abbyniewchas/heart_valve_bioreactor/designs/Full System CAD/Pressure Sensor V2/Assem3.PNG

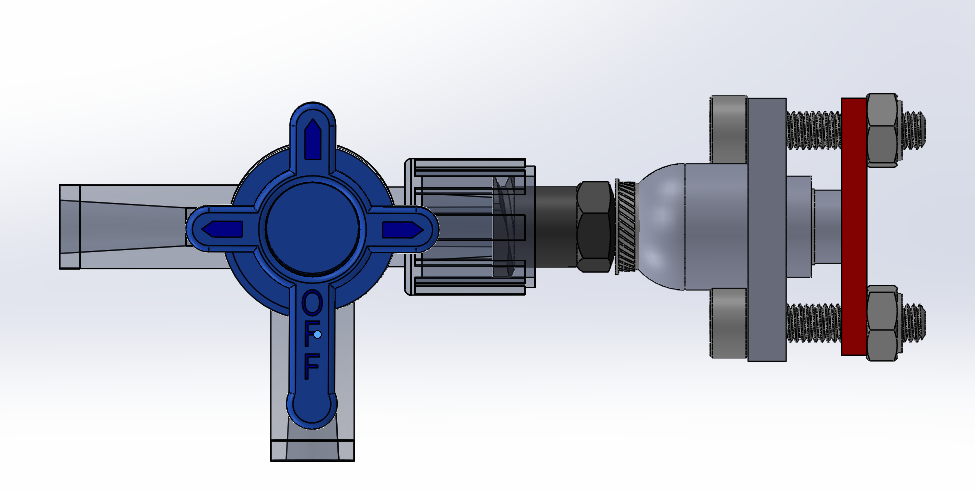
designs/Full System CAD/Pressure Sensor V2/Assem3.PNG
