abbyniewchas/heart_valve_bioreactor/matlab/data_acquisition/waveform_fig.jpg

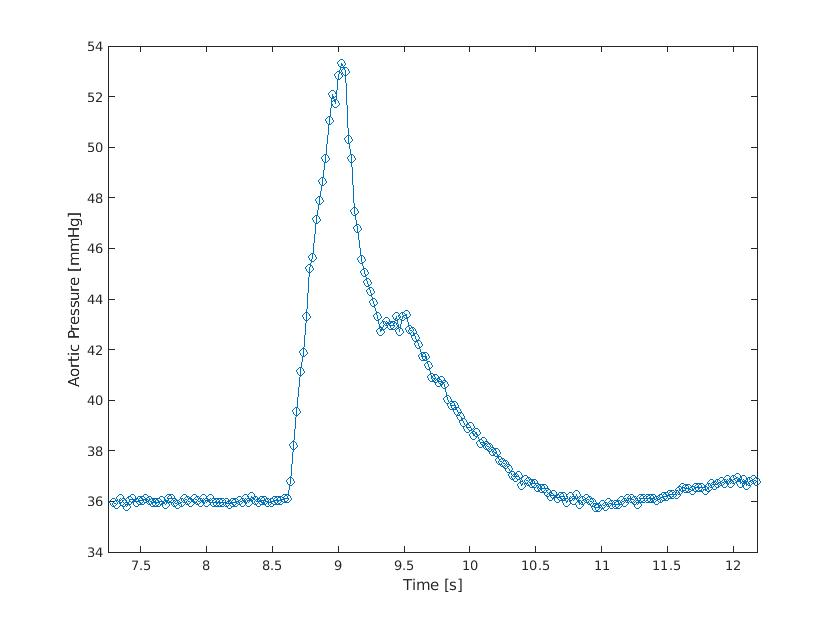
matlab/data_acquisition/waveform_fig.jpg
