abbyniewchas/heart_valve_bioreactor/designs/Full System CAD/Tubing and fittings/Media exchange fittings.SLDASM

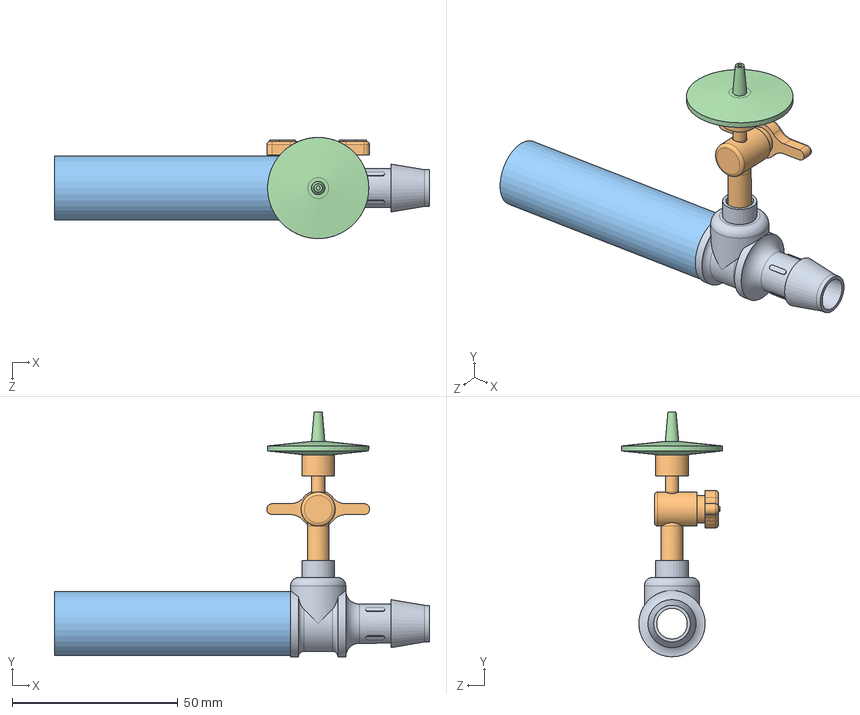
[picture p33: CAD file, 2020-04-21]
designs/Full System CAD/Tubing and fittings/Media exchange fittings.SLDASM
113.0 x 73.7 x 30.5 mm
.5in tubing to .5in tubing to male luer tee fitting
Stopcock (from grabcad)
Check valve to pump
Sterile filter
