abbyniewchas/heart_valve_bioreactor/designs/Full System CAD/Tubing and fittings/Check-ALL valve with fittings.SLDASM

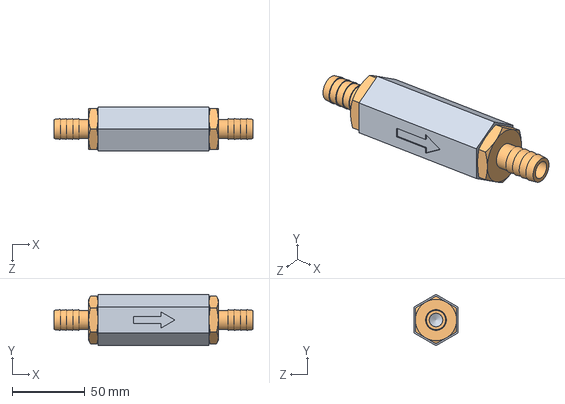
[picture p34: CAD file, 2020-04-21]
designs/Full System CAD/Tubing and fittings/Check-ALL valve with fittings.SLDASM
136.4 x 35.2 x 30.5 mm
Checkk-ALL check valve
three quarter NPT to half in tube x 2
