abbyniewchas/heart_valve_bioreactor/designs/Full System CAD/Current pump/Full pump assembly.SLDASM

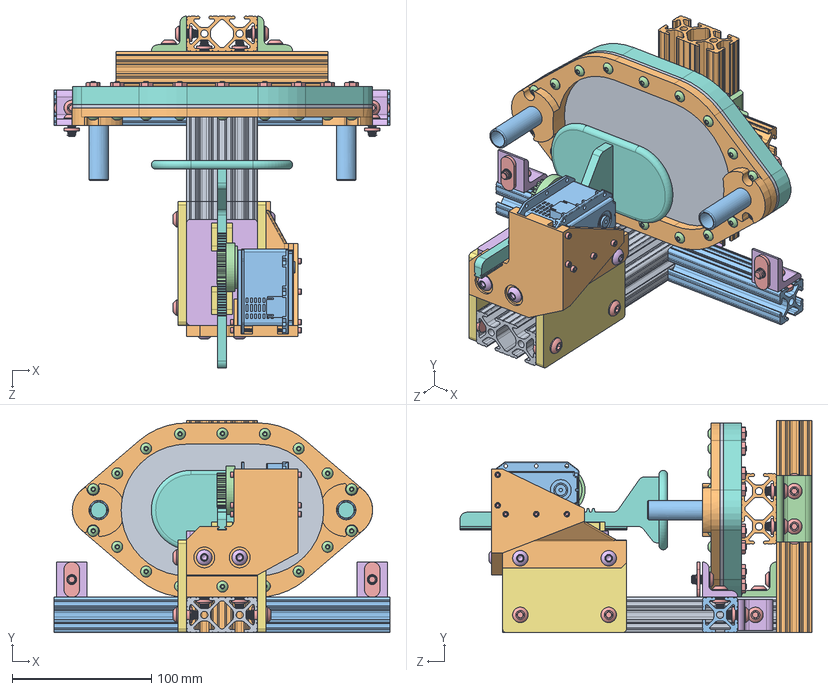
[picture p35: CAD file, 2020-04-21]
designs/Full System CAD/Current pump/Full pump assembly.SLDASM
241.3 x 152.4 x 252.9 mm
47065T418_ALUMINUM T-SLOTTED FRAMING EXTRUSION
80_20 double 6in x 2
80_20 3.75in x 2
80_20 L bracket wide x 3
80_20 fastening screw x 27
80_20 L-bracket small x 4
pump acrylic aligner x 2
Pump membrane backing
Pump membrane
Pump membrane front
Pump membrane fitting x 2
membrane screw x 18
membrane nut x 18
Acrylic topper
rack mount x 2
Pump piston rack
80_20 double 3.5in
Motor mount
MX-64 Motor (from grabacad)
Pump pinion
motor mount screw x 8
.25-20 extra screw x 4
pinion mounting screw
