abbyniewchas/heart_valve_bioreactor/designs/Full System CAD/Pump redesign concept/redesigned piston assembly.SLDASM

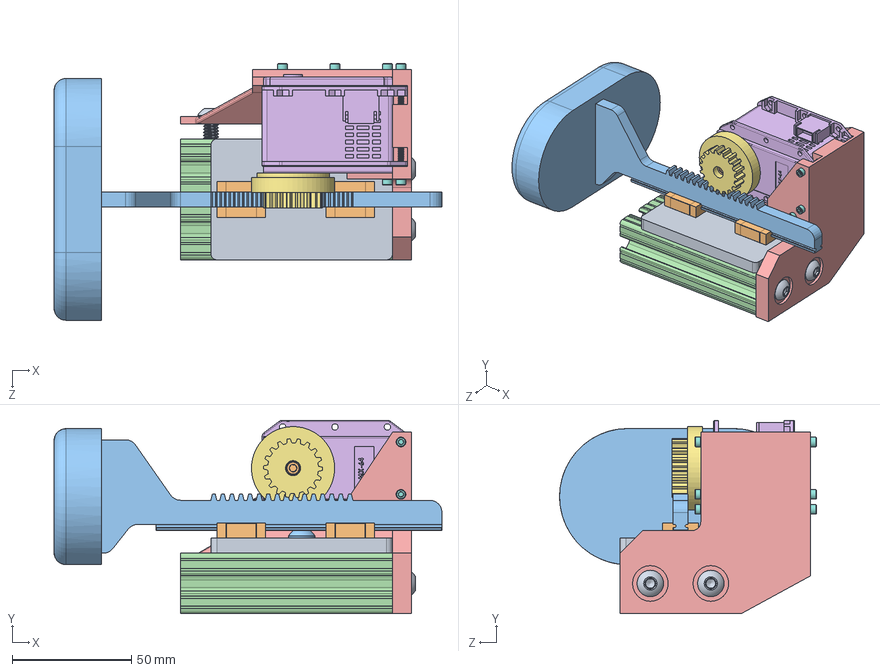
[picture p36: CAD file, 2020-04-21]
designs/Full System CAD/Pump redesign concept/redesigned piston assembly.SLDASM
162.9 x 81.2 x 107.8 mm
Acrylic topper
rack mount x 2
redesigned pump piston rack + paddle
80_20 double 3.5in
Motor mount
MX-64 Motor (from grabacad)
Pump pinion
motor mount screw x 8
.25-20 extra screw x 4
pinion mounting screw
80_20 fastening screw
