abbyniewchas/heart_valve_bioreactor/designs/Full System CAD/Tubing and fittings/Compliance Chamber top fitting.SLDASM

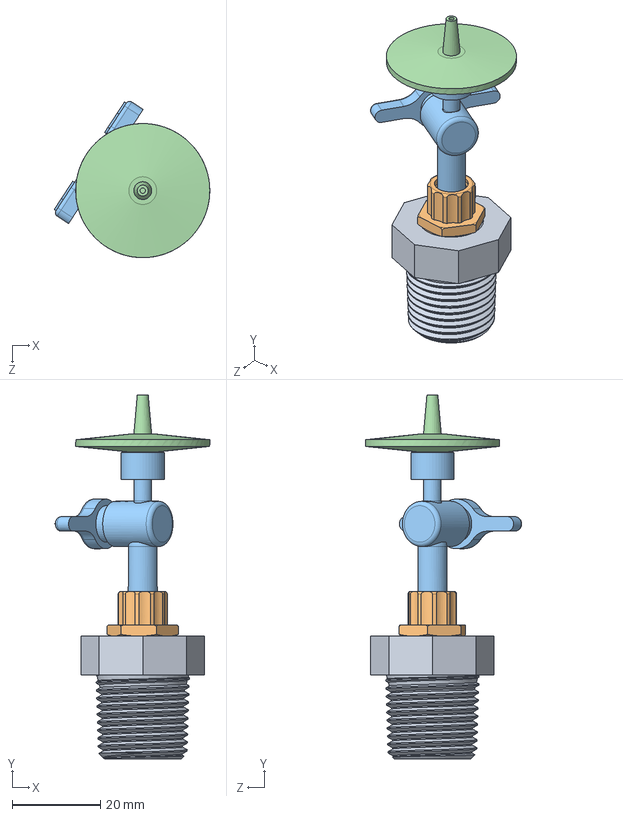
[picture p37: CAD file, 2020-04-21]
designs/Full System CAD/Tubing and fittings/Compliance Chamber top fitting.SLDASM
35.4 x 82.7 x 35.5 mm
4880K343_1-2NPTmale-to-1-4NPTfemale
51525K437_1-4NPT-to-Luer
Stopcock (from grabcad)
Sterile filter
