abbyniewchas/heart_valve_bioreactor/designs/Full System CAD/Frame/MR Mount asm.SLDASM

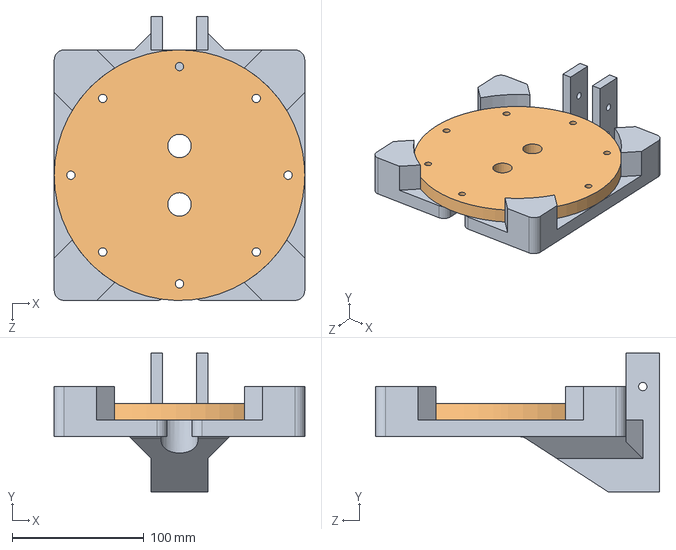
[picture p38: CAD file, 2020-04-21]
designs/Full System CAD/Frame/MR Mount asm.SLDASM
190.5 x 105.4 x 215.9 mm
Media Reservoir Mount
Media reservoir modified bottom
