abbyniewchas/heart_valve_bioreactor/designs/Full System CAD/Pump redesign concept/Redesigned full pump assembly.SLDASM

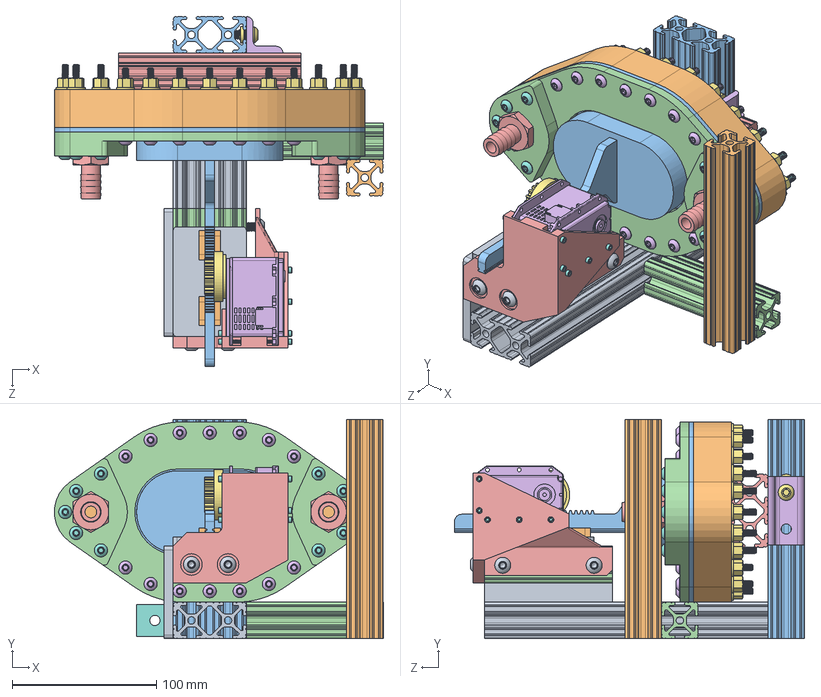
[picture p39: CAD file, 2020-04-21]
designs/Full System CAD/Pump redesign concept/Redesigned full pump assembly.SLDASM
228.5 x 152.4 x 243.0 mm
redesigned pump membrane backing
redesigned pump membrane
redesigned membrane front
half NPT to half in tube x 2
91255A252_membrane screw x 14
membrane nut 10_24 x 24
91255A813_membrane screw long x 10
Acrylic topper
rack mount x 2
redesigned pump piston rack + paddle
80_20 double 3.5in
Motor mount
MX-64 Motor (from grabacad)
Pump pinion
motor mount screw x 8
.25-20 extra screw x 4
pinion mounting screw
80_20 fastening screw
