abbyniewchas/heart_valve_bioreactor/designs/Full System CAD/Frame/80_20 Frame.SLDASM

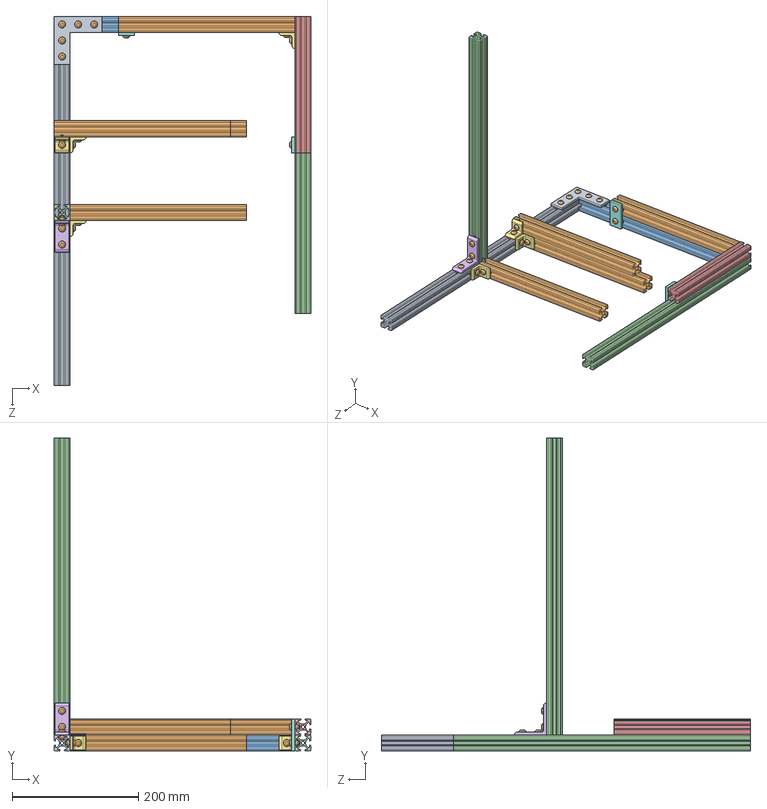
[picture p40: CAD file, 2020-04-21]
designs/Full System CAD/Frame/80_20 Frame.SLDASM
406.4 x 495.3 x 584.2 mm
80_20 23in
80_20 11in x 4
80_20 14in
80_20 18.5in x 2
80_20 8.5in
80_20 L Bracket long
80_20 L-bracket small x 4
80_20 straight fastener x 2
80_20 Corner fastener
80_20 fastening screw x 21
