abbyniewchas/heart_valve_bioreactor/designs/Full System CAD/Frame/CC mount am.SLDASM

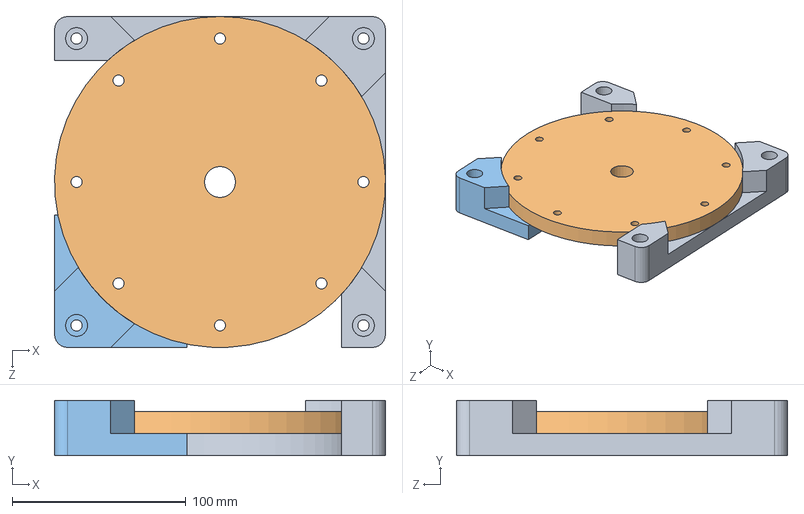
[picture p41: CAD file, 2020-04-21]
designs/Full System CAD/Frame/CC mount am.SLDASM
190.5 x 31.8 x 190.5 mm
CC Mount redesign pt 2
Top + bottom of CC
CC Mount redesign pt 1
