abbyniewchas/heart_valve_bioreactor/designs/Full System CAD/Compliance Chamber/CAD/FINAL DESIGN/316 SS THREADED ROD.SLDPRT

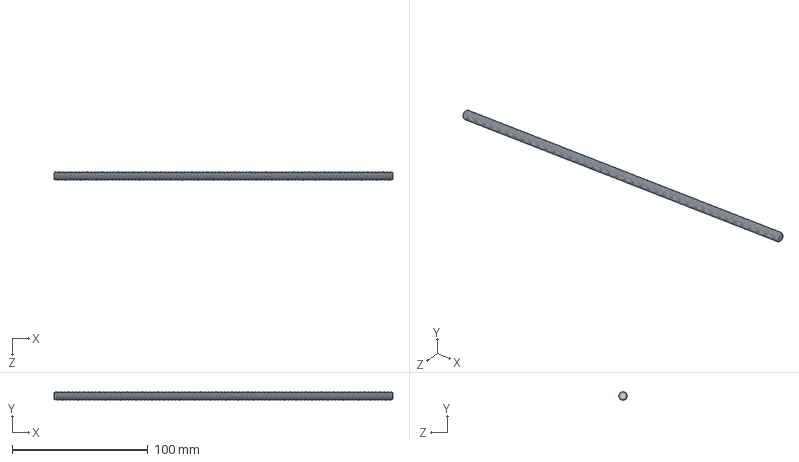
[picture p42: CAD file, 2020-04-21]
designs/Full System CAD/Compliance Chamber/CAD/FINAL DESIGN/316 SS THREADED ROD.SLDPRT
250.2 x 6.35 x 6.35 mm
