abbyniewchas/heart_valve_bioreactor/designs/Full System CAD/Compliance Chamber/CAD/Initial Design/Bottom cap.SLDPRT

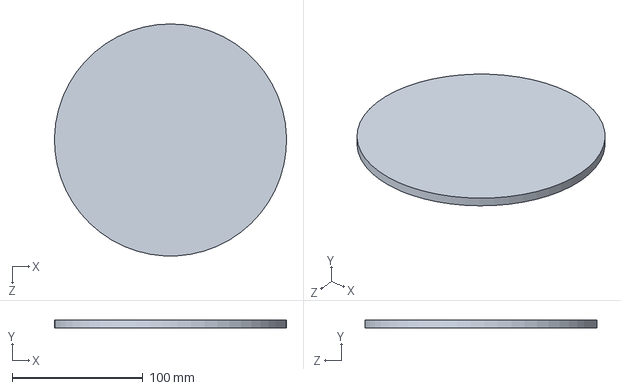
[picture p43: CAD file, 2020-04-21]
designs/Full System CAD/Compliance Chamber/CAD/Initial Design/Bottom cap.SLDPRT
177.7 x 6.35 x 177.8 mm
