abbyniewchas/heart_valve_bioreactor/designs/Full System CAD/Compliance Chamber/Initial simulation mock-up/Compliance chamber for pressure sim.SLDPRT

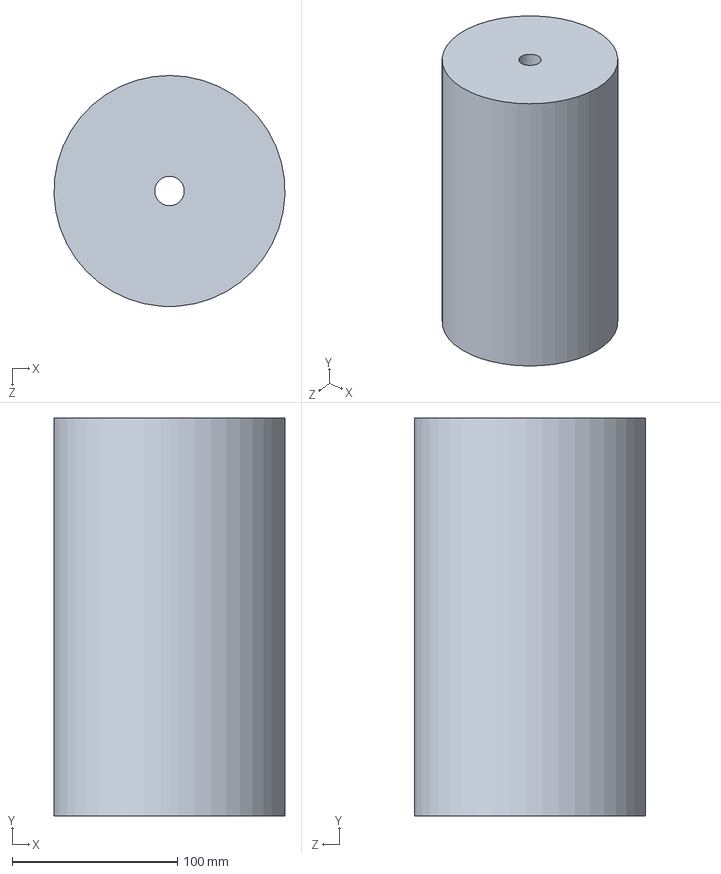
[picture p44: CAD file, 2020-04-21]
designs/Full System CAD/Compliance Chamber/Initial simulation mock-up/Compliance chamber for pressure sim.SLDPRT
139.6 x 240.7 x 139.7 mm
