abbyniewchas/heart_valve_bioreactor/designs/Full System CAD/Current pump/rack mount.SLDPRT

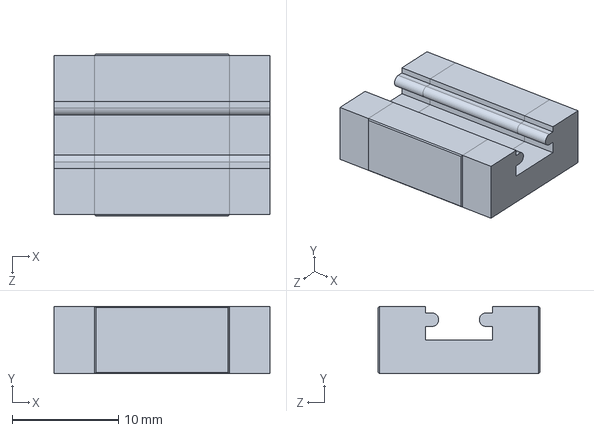
[picture p45: CAD file, 2020-04-21]
designs/Full System CAD/Current pump/rack mount.SLDPRT
20.3 x 6.35 x 15.2 mm
