abbyniewchas/heart_valve_bioreactor/designs/Full System CAD/media reservoir/MR walls.SLDPRT

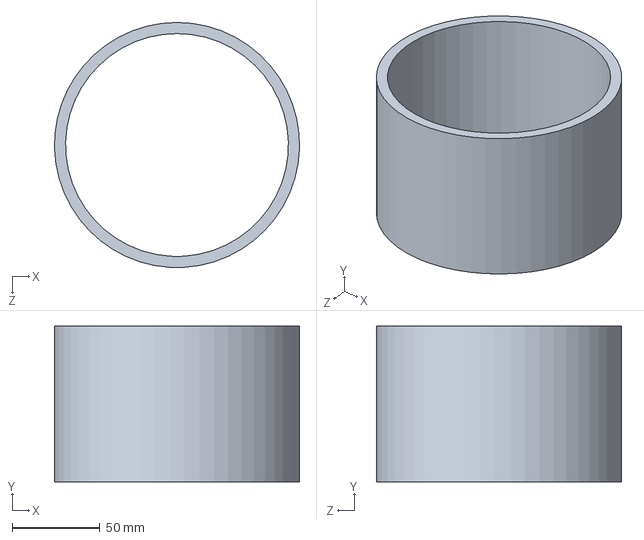
[picture p46: CAD file, 2020-04-21]
designs/Full System CAD/media reservoir/MR walls.SLDPRT
139.6 x 88.9 x 139.7 mm
