abbyniewchas/heart_valve_bioreactor/designs/Full System CAD/Processing_chamber/Top_V2.SLDPRT

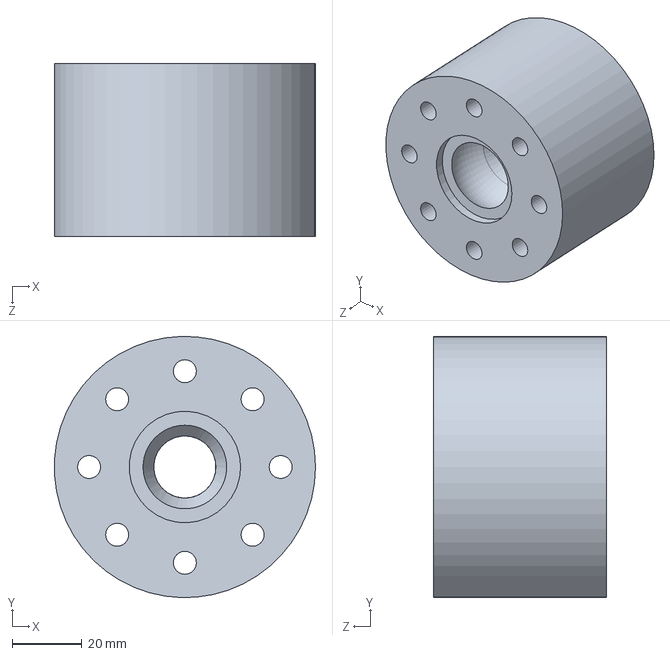
[picture p47: CAD file, 2020-04-21]
designs/Full System CAD/Processing_chamber/Top_V2.SLDPRT
74.9 x 75.0 x 49.7 mm
