abbyniewchas/heart_valve_bioreactor/designs/Full System CAD/Pump redesign concept/Motor mount.SLDPRT

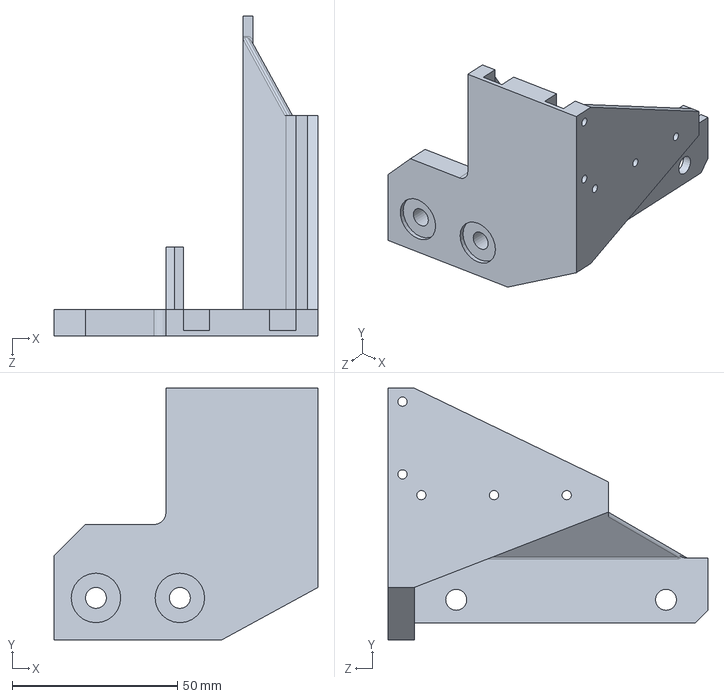
[picture p48: CAD file, 2020-04-21]
designs/Full System CAD/Pump redesign concept/Motor mount.SLDPRT
79.9 x 76.2 x 96.8 mm
