abbyniewchas/heart_valve_bioreactor/designs/Pressure transducer /Capsulev1.SLDPRT

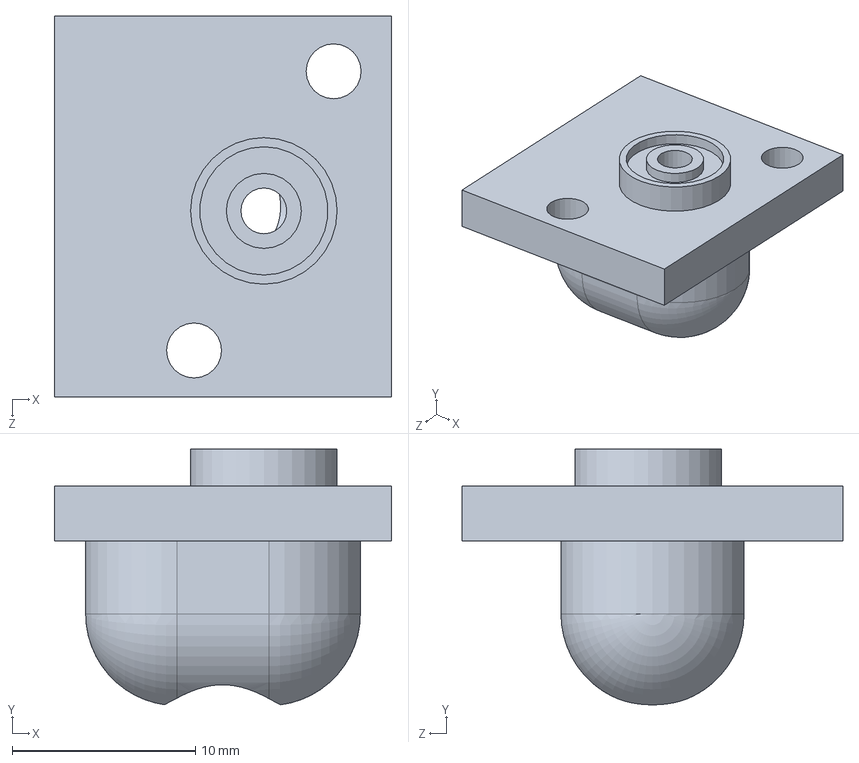
[picture p49: CAD file, 2020-04-21]
designs/Pressure transducer /Capsulev1.SLDPRT
18.4 x 14.0 x 20.8 mm
