abbyniewchas/heart_valve_bioreactor/designs/Pressure transducer /PressureSensorv2/Stopcock Medex 3-way Hi-Flo 1931-1L.SLDPRT

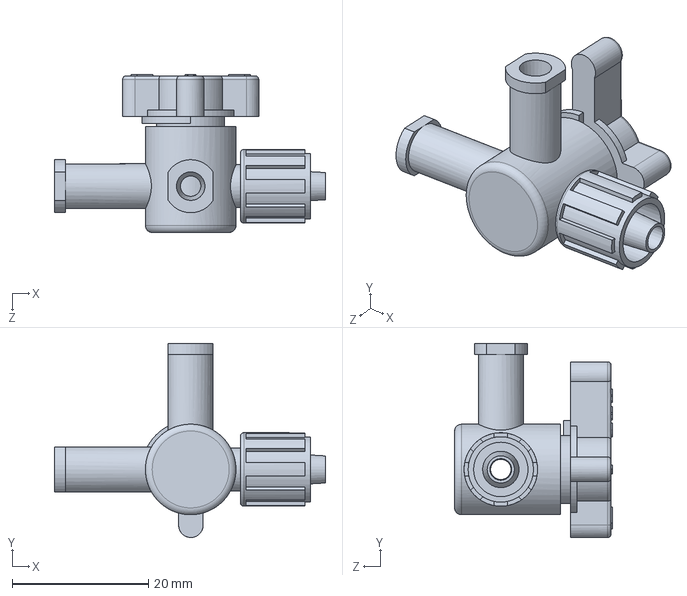
[picture p50: CAD file, 2020-04-21]
designs/Pressure transducer /PressureSensorv2/Stopcock Medex 3-way Hi-Flo 1931-1L.SLDPRT
39.8 x 28.5 x 23.2 mm
