abbyniewchas/heart_valve_bioreactor/designs/Full System CAD/Current pump/Pump membrane.SLDPRT

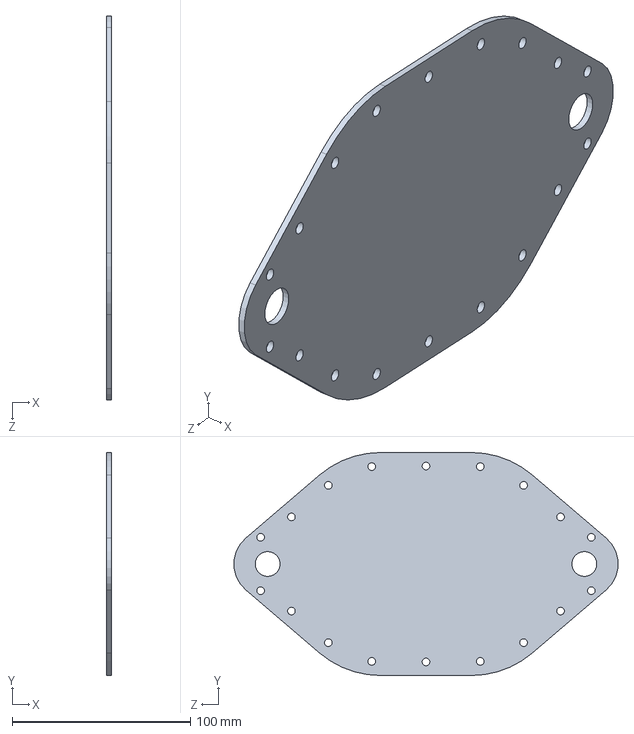
[picture p51: CAD file, 2020-04-21]
designs/Full System CAD/Current pump/Pump membrane.SLDPRT
2.54 x 125.2 x 215.6 mm
