abbyniewchas/heart_valve_bioreactor/designs/Full System CAD/Frame/PC Mount pt2.SLDPRT

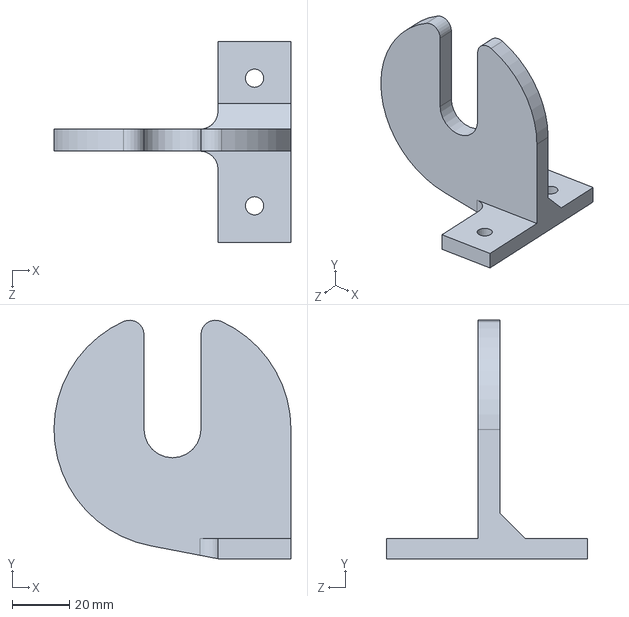
[picture p52: CAD file, 2020-04-21]
designs/Full System CAD/Frame/PC Mount pt2.SLDPRT
82.5 x 83.1 x 69.8 mm
