abbyniewchas/heart_valve_bioreactor/designs/Full System CAD/media reservoir/Media reservoir modified bottom.SLDPRT

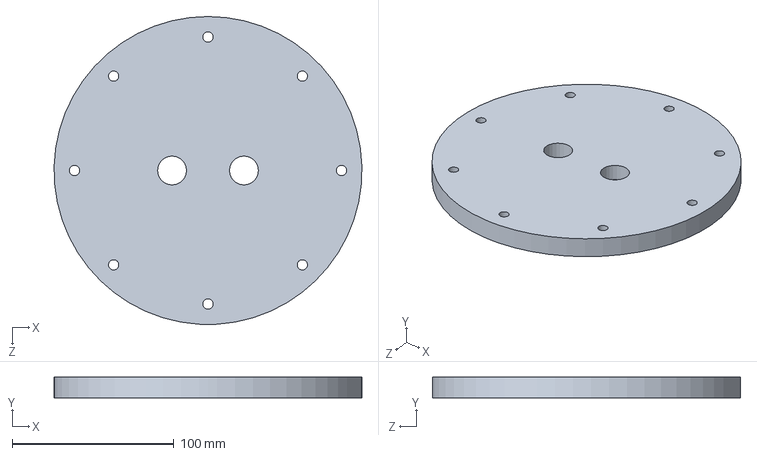
[picture p53: CAD file, 2020-04-21]
designs/Full System CAD/media reservoir/Media reservoir modified bottom.SLDPRT
190.4 x 12.7 x 190.5 mm
