abbyniewchas/heart_valve_bioreactor/designs/Full System CAD/Processing_chamber/Top.SLDPRT

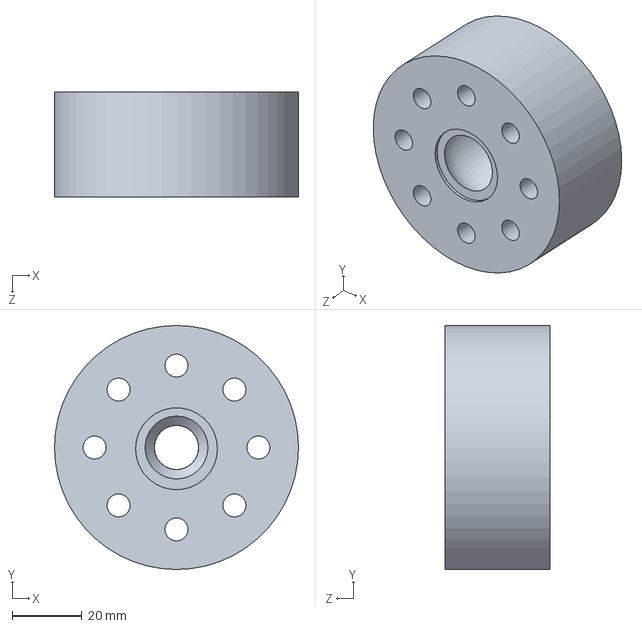
[picture p54: CAD file, 2020-04-21]
designs/Full System CAD/Processing_chamber/Top.SLDPRT
70.0 x 70.0 x 30.0 mm
