abbyniewchas/heart_valve_bioreactor/designs/Full System CAD/Pump redesign concept/80_20 double 5in.SLDPRT

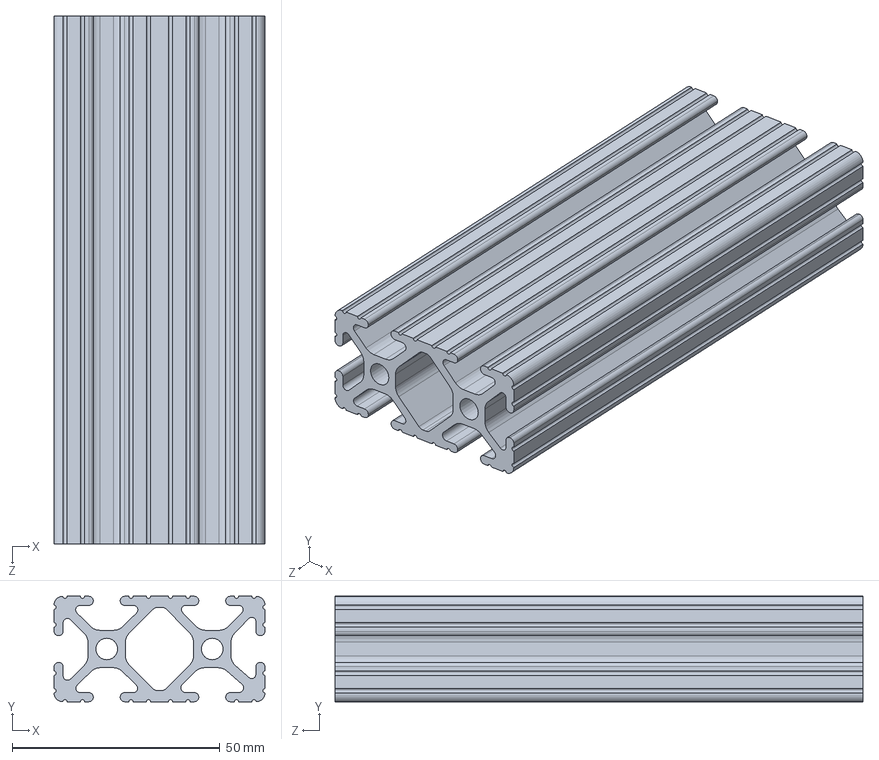
[picture p55: CAD file, 2020-04-21]
designs/Full System CAD/Pump redesign concept/80_20 double 5in.SLDPRT
50.8 x 25.4 x 127.0 mm
