abbyniewchas/heart_valve_bioreactor/designs/Full System CAD/Tubing and fittings/Check valve to pump.SLDPRT

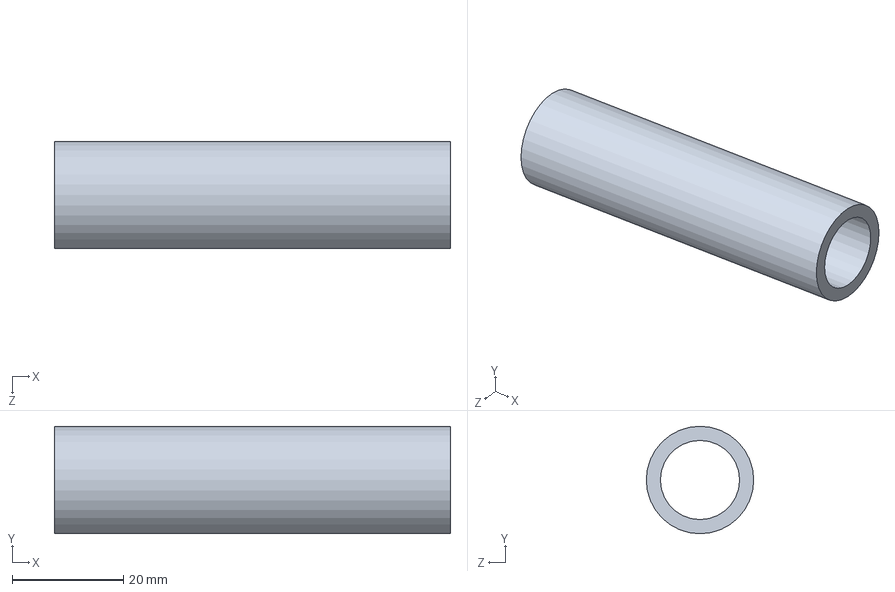
[picture p56: CAD file, 2020-04-21]
designs/Full System CAD/Tubing and fittings/Check valve to pump.SLDPRT
71.1 x 19.3 x 19.3 mm
