abbyniewchas/heart_valve_bioreactor/designs/Pressure transducer /PressureSensorv2/PressureSensor.SLDPRT

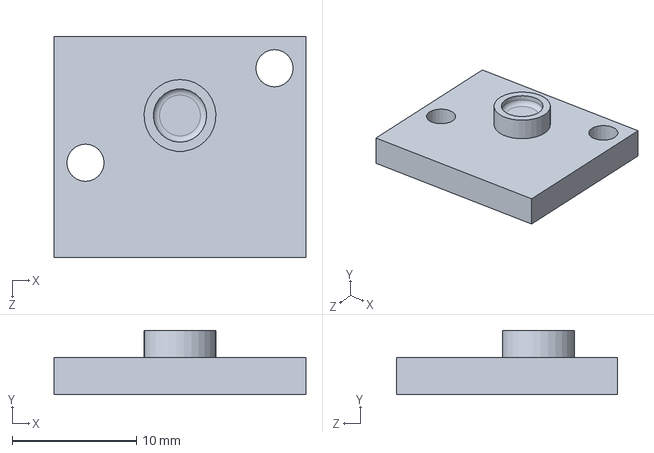
[picture p57: CAD file, 2020-04-21]
designs/Pressure transducer /PressureSensorv2/PressureSensor.SLDPRT
20.3 x 5.20 x 17.8 mm
