abbyniewchas/heart_valve_bioreactor/designs/Back Pressure/Solidworks/Top Cap.SLDPRT

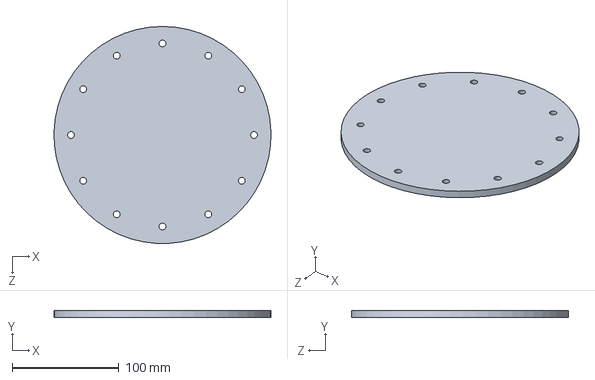
[picture p58: CAD file, 2020-04-21]
designs/Back Pressure/Solidworks/Top Cap.SLDPRT
203.1 x 6.35 x 203.2 mm
