abbyniewchas/heart_valve_bioreactor/designs/Full System CAD/Current pump/MX-64 Motor (from grabacad).SLDPRT

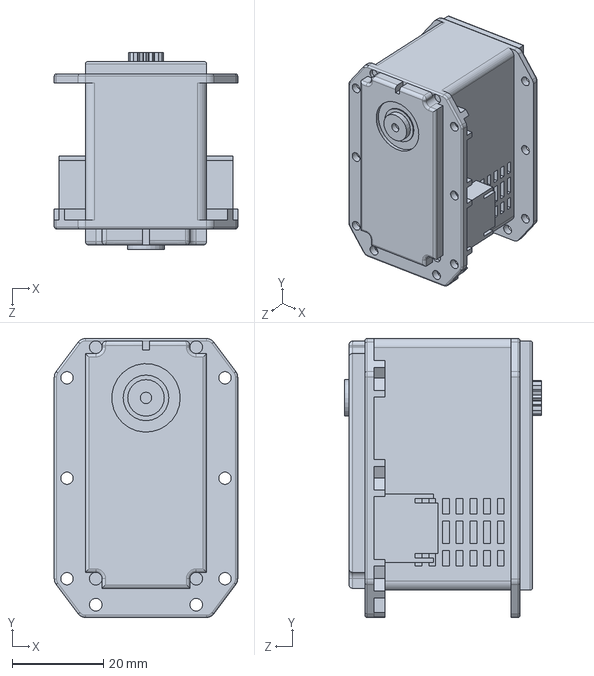
[picture p59: CAD file, 2020-04-21]
designs/Full System CAD/Current pump/MX-64 Motor (from grabacad).SLDPRT
40.2 x 61.1 x 43.2 mm
