abbyniewchas/heart_valve_bioreactor/designs/Full System CAD/media reservoir/Threaded rod 5in.SLDPRT

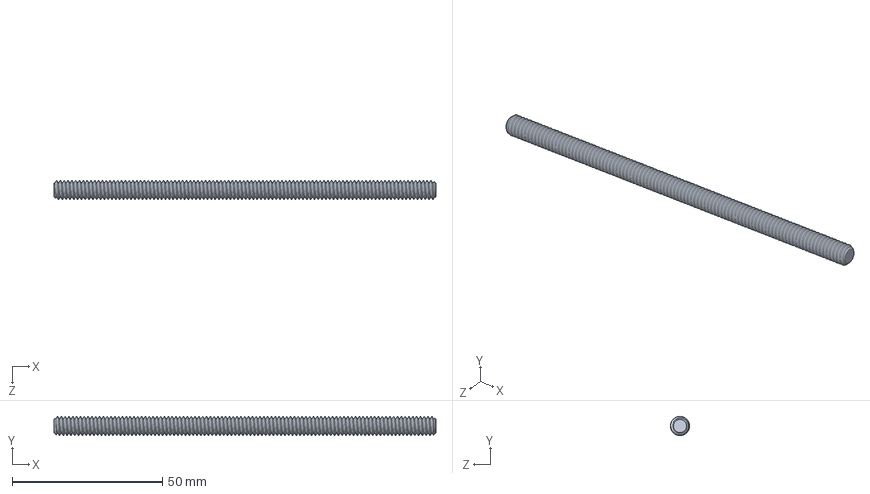
[picture p60: CAD file, 2020-04-21]
designs/Full System CAD/media reservoir/Threaded rod 5in.SLDPRT
127.0 x 6.35 x 6.35 mm
