abbyniewchas/heart_valve_bioreactor/designs/Full System CAD/Tubing and fittings/.5in tubing to .5in tubing to male luer tee fitting.SLDPRT

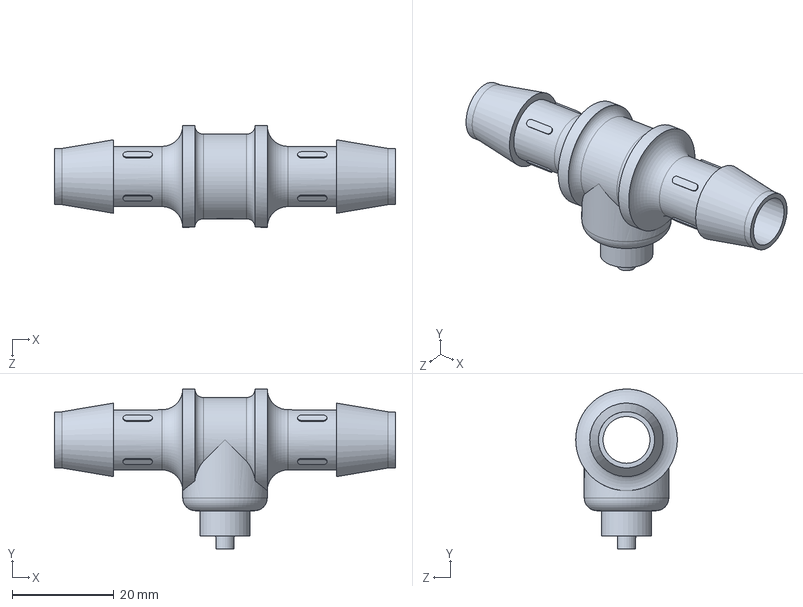
[picture p61: CAD file, 2020-04-21]
designs/Full System CAD/Tubing and fittings/.5in tubing to .5in tubing to male luer tee fitting.SLDPRT
67.1 x 31.4 x 20.0 mm
