abbyniewchas/heart_valve_bioreactor/designs/Full System CAD/Compliance Chamber/CAD/Initial Design/Flange.SLDPRT

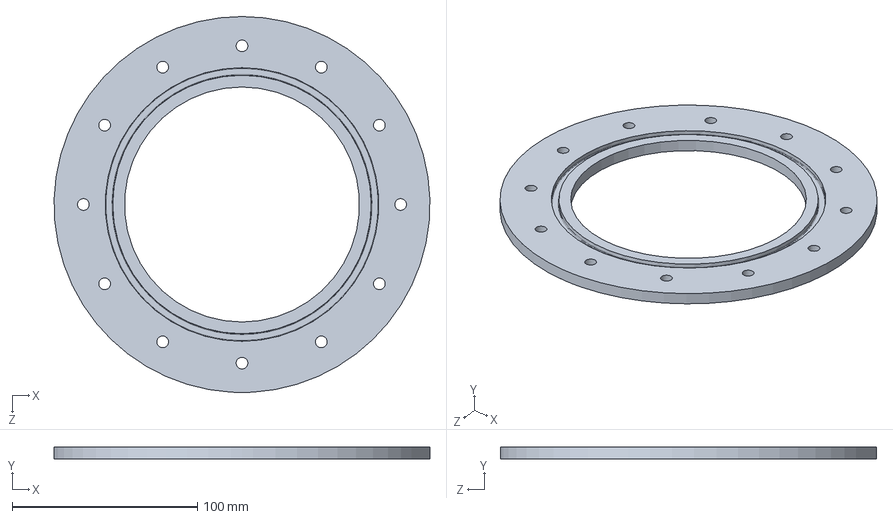
[picture p62: CAD file, 2020-04-21]
designs/Full System CAD/Compliance Chamber/CAD/Initial Design/Flange.SLDPRT
203.1 x 6.35 x 203.2 mm
