abbyniewchas/heart_valve_bioreactor/designs/Full System CAD/Compliance Chamber/Initial simulation mock-up/Compliance chamber seal.SLDPRT

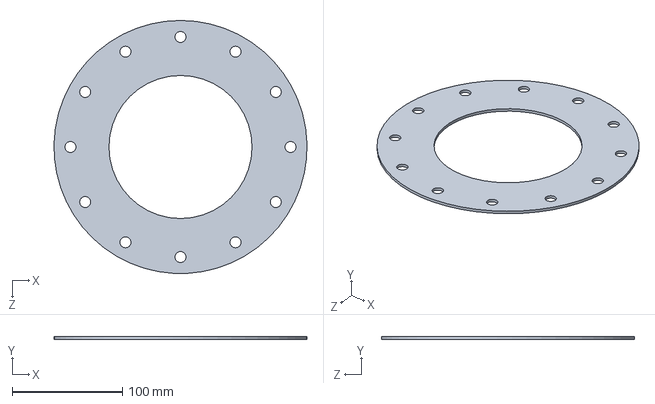
[picture p63: CAD file, 2020-04-21]
designs/Full System CAD/Compliance Chamber/Initial simulation mock-up/Compliance chamber seal.SLDPRT
229.9 x 2.50 x 230.0 mm
