abbyniewchas/heart_valve_bioreactor/designs/Full System CAD/Frame/80_20 L-bracket small.SLDPRT

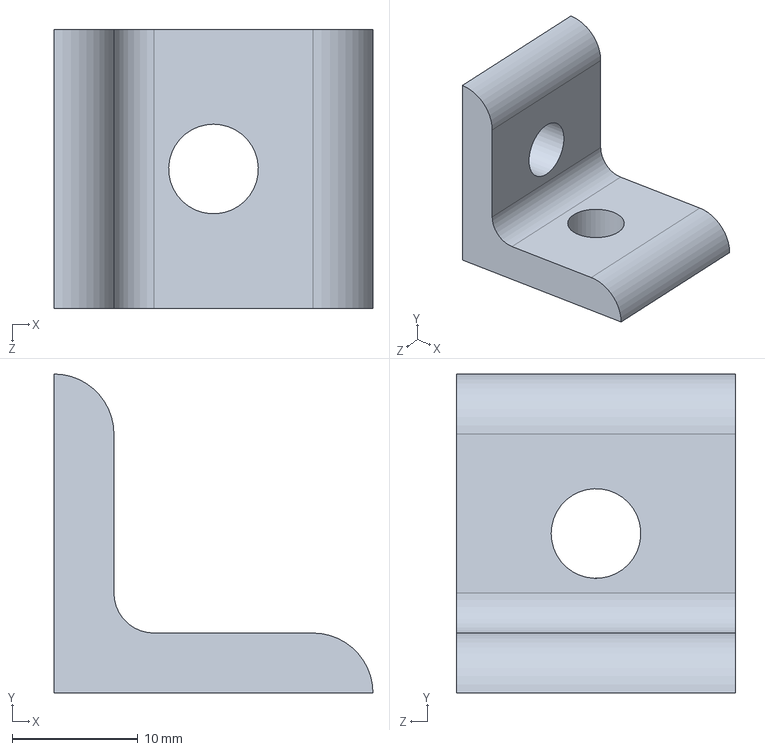
[picture p64: CAD file, 2020-04-21]
designs/Full System CAD/Frame/80_20 L-bracket small.SLDPRT
25.4 x 25.4 x 22.2 mm
