abbyniewchas/heart_valve_bioreactor/designs/Full System CAD/Pressure Sensor V2/Capsulev2.SLDPRT

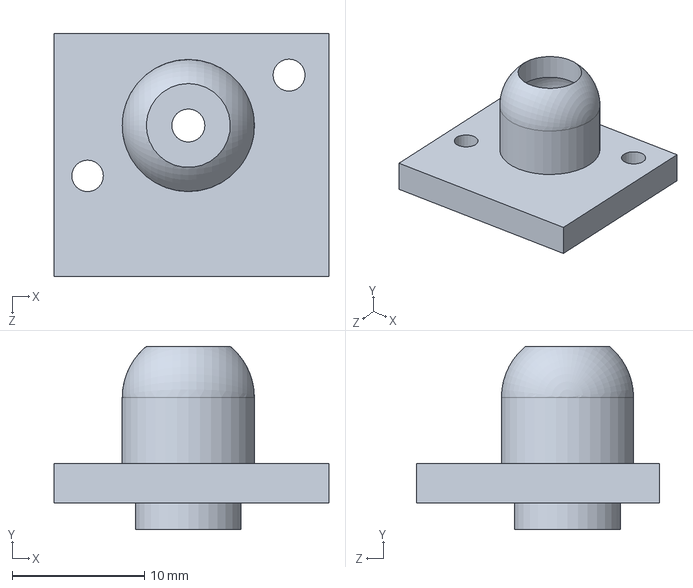
[picture p65: CAD file, 2020-04-21]
designs/Full System CAD/Pressure Sensor V2/Capsulev2.SLDPRT
20.8 x 13.9 x 18.4 mm
