abbyniewchas/heart_valve_bioreactor/designs/Full System CAD/Processing_chamber/Heart_Valve.SLDPRT

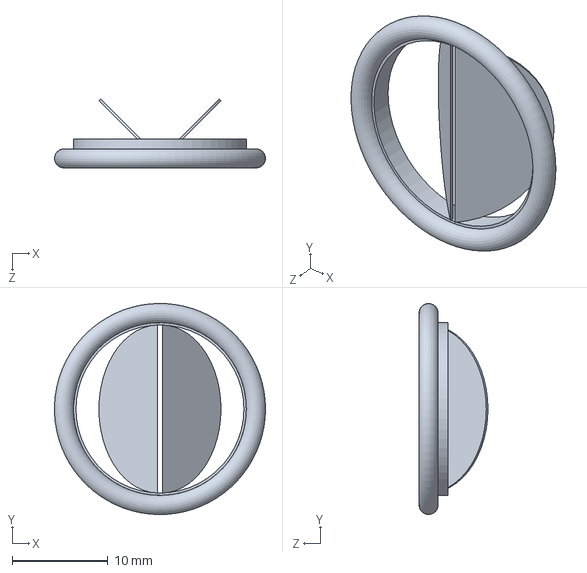
[picture p66: CAD file, 2020-04-21]
designs/Full System CAD/Processing_chamber/Heart_Valve.SLDPRT
22.0 x 22.0 x 7.19 mm
