abbyniewchas/heart_valve_bioreactor/designs/Full System CAD/Tubing and fittings/PT to CC.SLDPRT

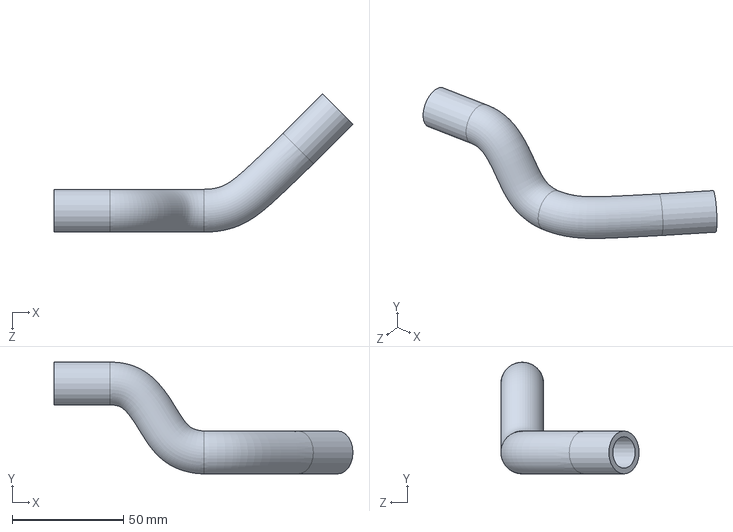
[picture p67: CAD file, 2020-04-21]
designs/Full System CAD/Tubing and fittings/PT to CC.SLDPRT
134.5 x 50.3 x 62.2 mm
