abbyniewchas/heart_valve_bioreactor/designs/Full System CAD/Frame/80_20 straight fastener.SLDPRT

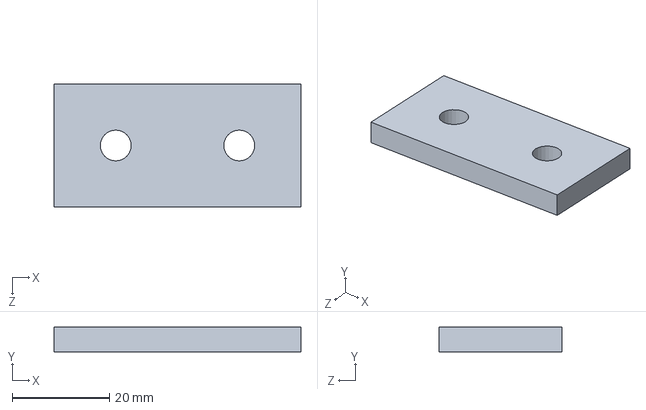
[picture p68: CAD file, 2020-04-21]
designs/Full System CAD/Frame/80_20 straight fastener.SLDPRT
50.8 x 5.08 x 25.4 mm
