abbyniewchas/heart_valve_bioreactor/designs/Full System CAD/Pump redesign concept/redesigned pump membrane backing.SLDPRT

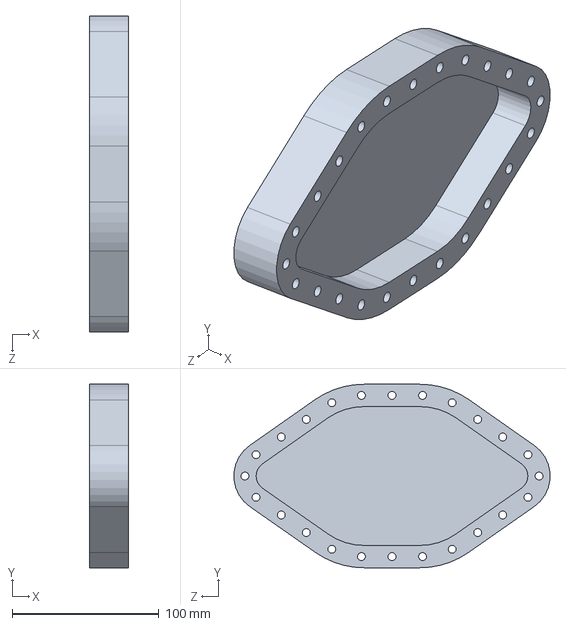
[picture p69: CAD file, 2020-04-21]
designs/Full System CAD/Pump redesign concept/redesigned pump membrane backing.SLDPRT
26.4 x 125.2 x 215.6 mm
