abbyniewchas/heart_valve_bioreactor/designs/Full System CAD/Compliance Chamber/Initial simulation mock-up/Compliance Chamber Cap.SLDPRT

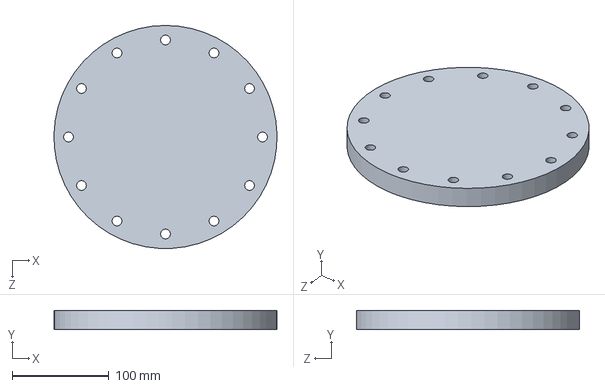
[picture p70: CAD file, 2020-04-21]
designs/Full System CAD/Compliance Chamber/Initial simulation mock-up/Compliance Chamber Cap.SLDPRT
229.9 x 20.0 x 230.0 mm
