abbyniewchas/heart_valve_bioreactor/designs/Full System CAD/Frame/PC Mount pt1.SLDPRT

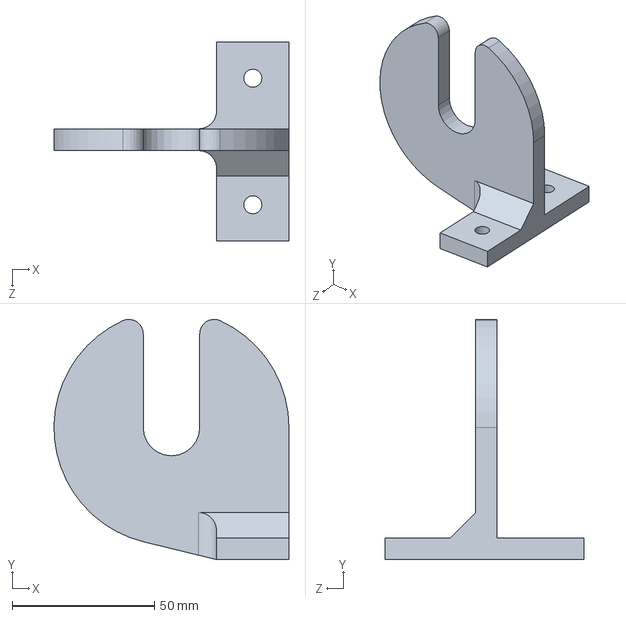
[picture p71: CAD file, 2020-04-21]
designs/Full System CAD/Frame/PC Mount pt1.SLDPRT
82.5 x 84.4 x 69.8 mm
