abbyniewchas/heart_valve_bioreactor/designs/Full System CAD/Compliance Chamber/Initial simulation mock-up/Compliance Chamber.SLDPRT

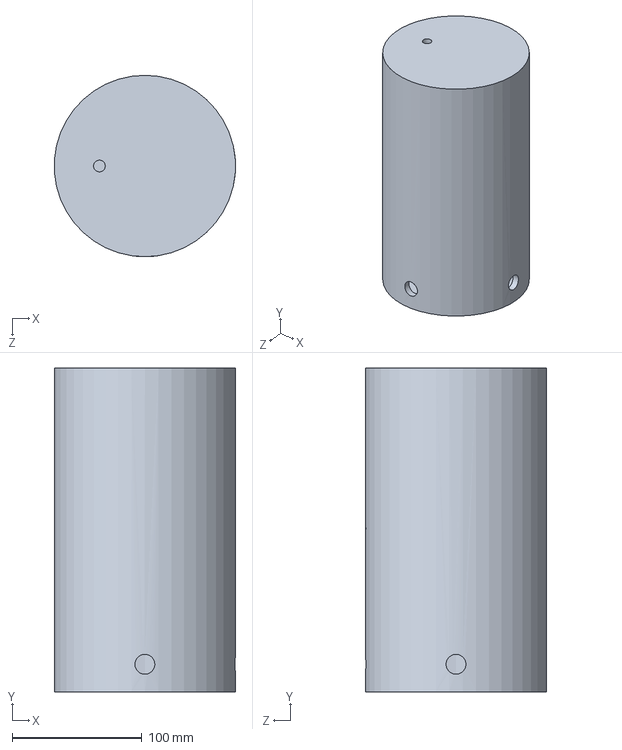
[picture p72: CAD file, 2020-04-21]
designs/Full System CAD/Compliance Chamber/Initial simulation mock-up/Compliance Chamber.SLDPRT
139.5 x 249.5 x 139.7 mm
