abbyniewchas/heart_valve_bioreactor/designs/Full System CAD/Frame/80_20 Corner fastener.SLDPRT

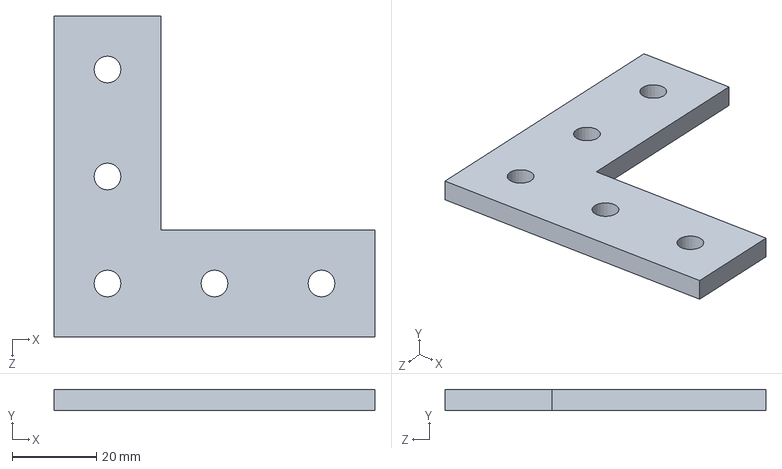
[picture p73: CAD file, 2020-04-21]
designs/Full System CAD/Frame/80_20 Corner fastener.SLDPRT
76.2 x 5.08 x 76.2 mm
