abbyniewchas/heart_valve_bioreactor/designs/Full System CAD/Tubing and fittings/Sterile filter.SLDPRT

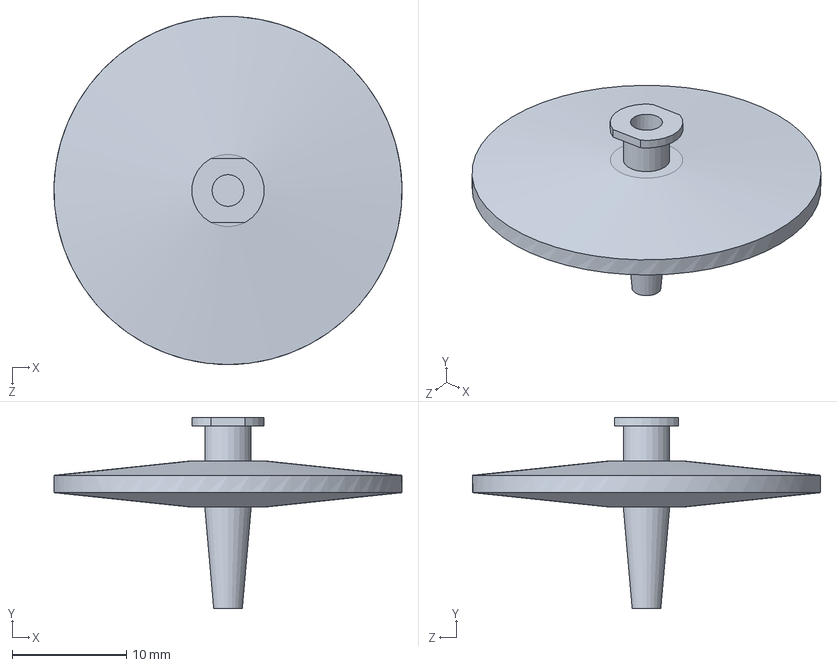
[picture p74: CAD file, 2020-04-21]
designs/Full System CAD/Tubing and fittings/Sterile filter.SLDPRT
30.5 x 16.8 x 30.5 mm
