abbyniewchas/heart_valve_bioreactor/designs/Full System CAD/Compliance Chamber/CAD/FINAL DESIGN/CC Bottom tee fitting.SLDPRT

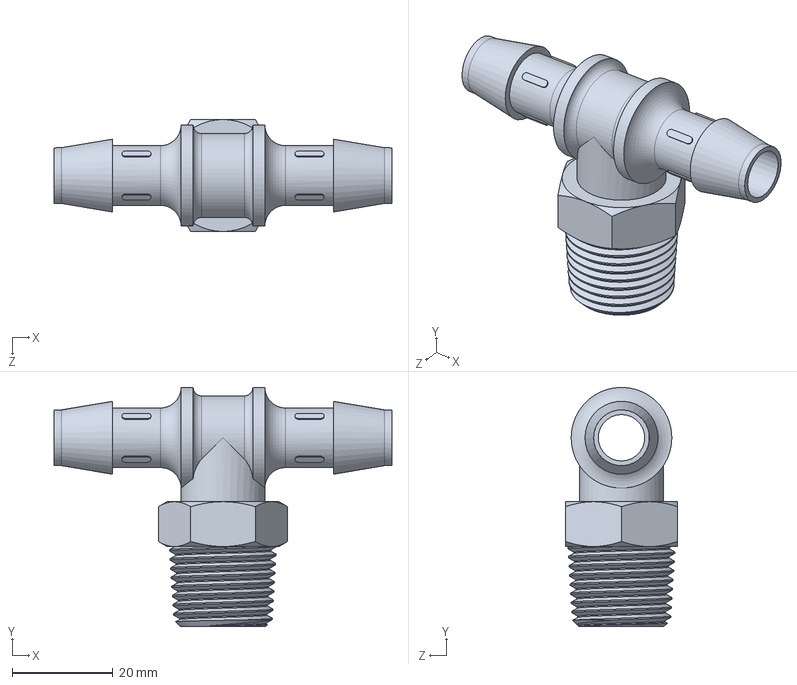
[picture p75: CAD file, 2020-04-21]
designs/Full System CAD/Compliance Chamber/CAD/FINAL DESIGN/CC Bottom tee fitting.SLDPRT
67.1 x 47.4 x 22.2 mm
