abbyniewchas/heart_valve_bioreactor/designs/Full System CAD/Processing_chamber/o-ring.SLDPRT

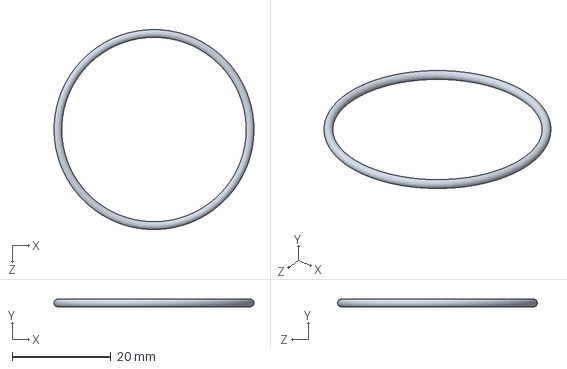
[picture p76: CAD file, 2020-04-21]
designs/Full System CAD/Processing_chamber/o-ring.SLDPRT
40.4 x 1.59 x 40.4 mm
