abbyniewchas/heart_valve_bioreactor/designs/Full System CAD/Current pump/Pump membrane fitting.SLDPRT

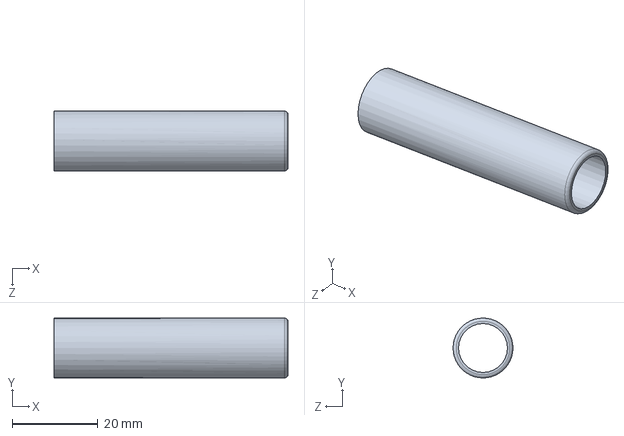
[picture p77: CAD file, 2020-04-21]
designs/Full System CAD/Current pump/Pump membrane fitting.SLDPRT
54.6 x 14.0 x 14.0 mm
