abbyniewchas/heart_valve_bioreactor/designs/Full System CAD/Frame/Media Reservoir Mount.SLDPRT

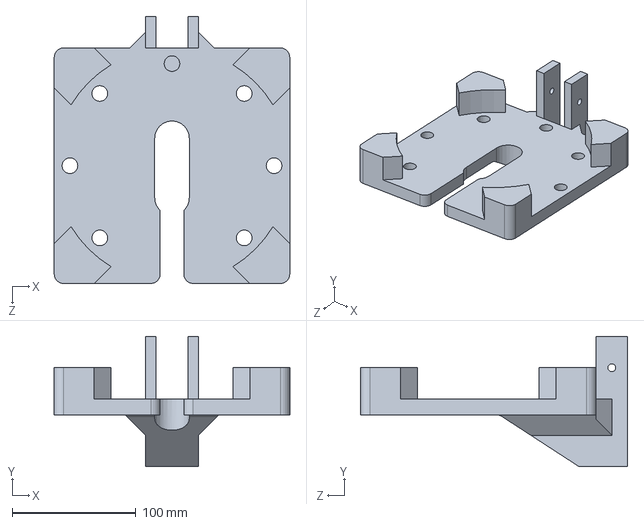
[picture p78: CAD file, 2020-04-21]
designs/Full System CAD/Frame/Media Reservoir Mount.SLDPRT
190.5 x 105.4 x 215.9 mm
