abbyniewchas/heart_valve_bioreactor/designs/Full System CAD/Tubing and fittings/pump to Pres. trans..SLDPRT

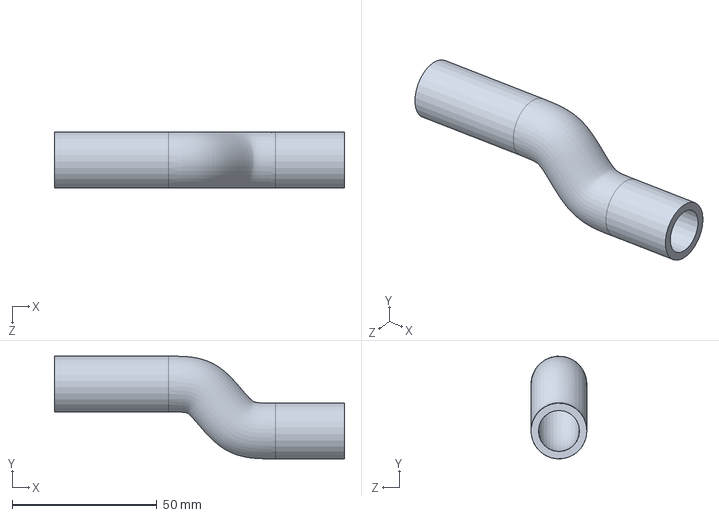
[picture p79: CAD file, 2020-04-21]
designs/Full System CAD/Tubing and fittings/pump to Pres. trans..SLDPRT
100.3 x 35.5 x 19.3 mm
