abbyniewchas/heart_valve_bioreactor/designs/Full System CAD/Current pump/Pump membrane backing.SLDPRT

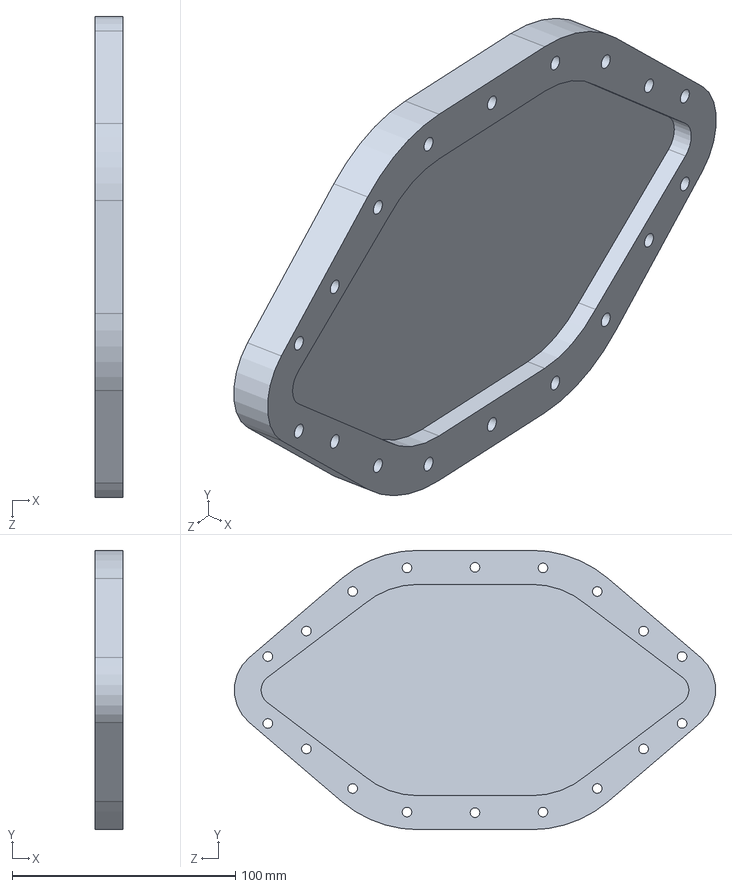
[picture p80: CAD file, 2020-04-21]
designs/Full System CAD/Current pump/Pump membrane backing.SLDPRT
12.7 x 125.2 x 215.6 mm
