abbyniewchas/heart_valve_bioreactor/designs/Full System CAD/Frame/MR mounting knob.SLDPRT

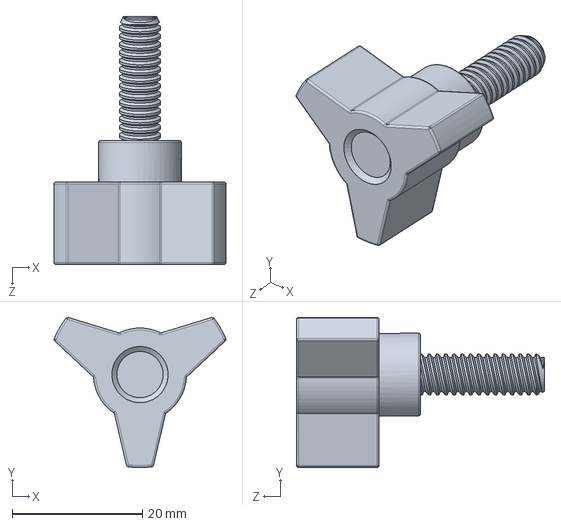
[picture p81: CAD file, 2020-04-21]
designs/Full System CAD/Frame/MR mounting knob.SLDPRT
26.4 x 23.1 x 38.1 mm
