abbyniewchas/heart_valve_bioreactor/designs/Full System CAD/Tubing and fittings/three quarter NPT to half in tube.SLDPRT

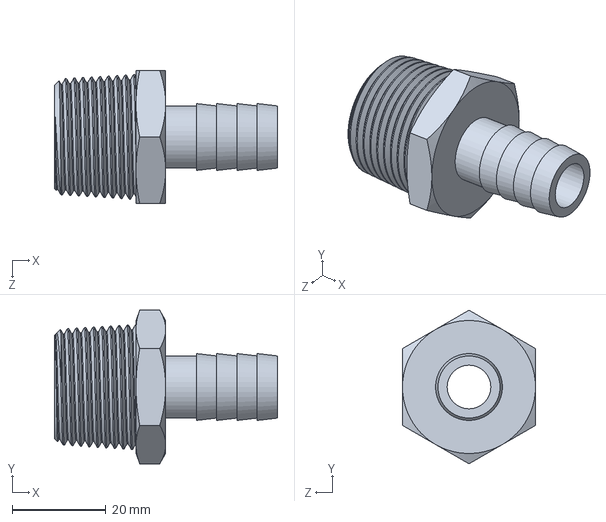
[picture p82: CAD file, 2020-04-21]
designs/Full System CAD/Tubing and fittings/three quarter NPT to half in tube.SLDPRT
47.5 x 32.7 x 28.3 mm
