abbyniewchas/heart_valve_bioreactor/designs/Full System CAD/Current pump/Pump pinion.SLDPRT

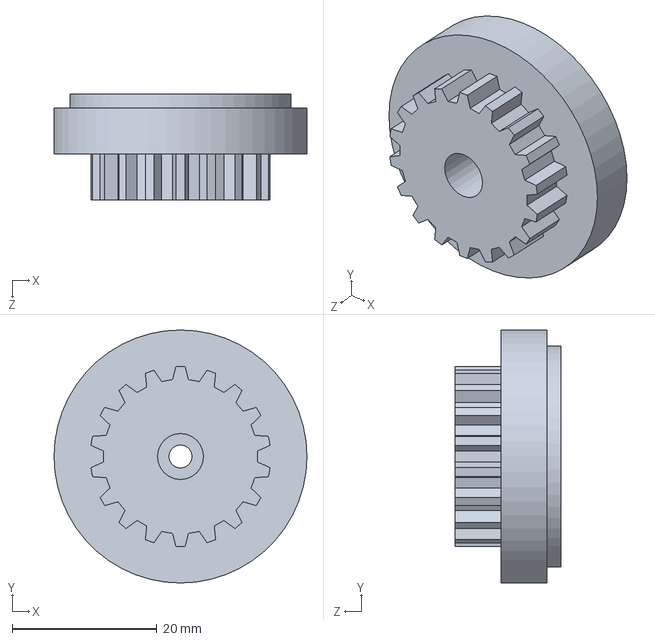
[picture p83: CAD file, 2020-04-21]
designs/Full System CAD/Current pump/Pump pinion.SLDPRT
34.9 x 34.9 x 14.7 mm
