abbyniewchas/heart_valve_bioreactor/designs/Full System CAD/Processing_chamber/Bottom.SLDPRT

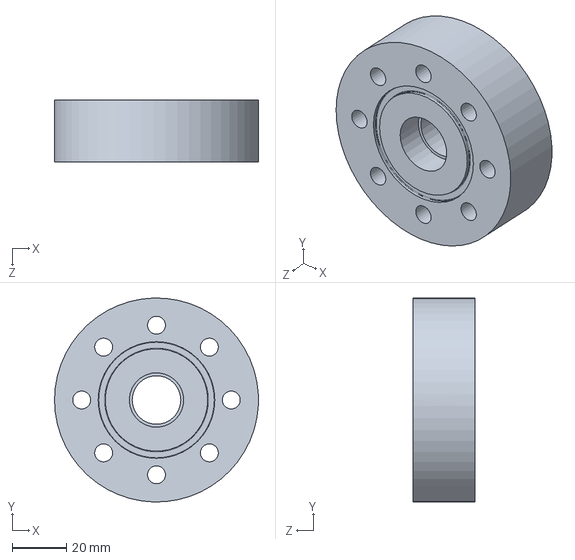
[picture p84: CAD file, 2020-04-21]
designs/Full System CAD/Processing_chamber/Bottom.SLDPRT
75.0 x 75.0 x 22.7 mm
