abbyniewchas/heart_valve_bioreactor/designs/Full System CAD/Pump redesign concept/Acrylic topper.SLDPRT

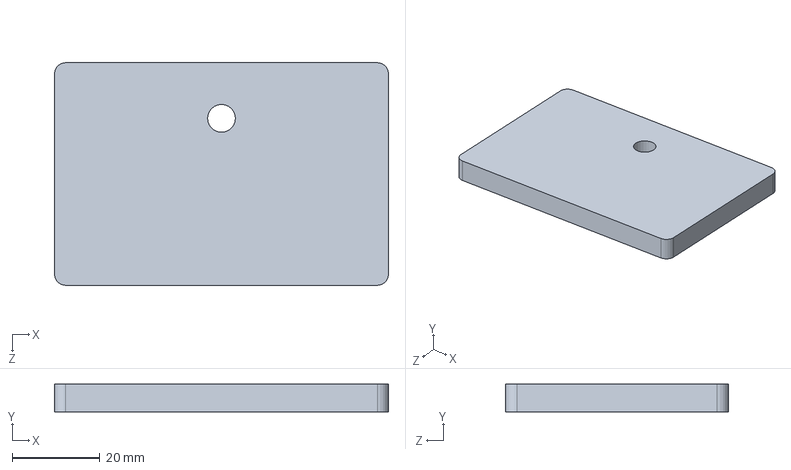
[picture p85: CAD file, 2020-04-21]
designs/Full System CAD/Pump redesign concept/Acrylic topper.SLDPRT
76.2 x 6.35 x 50.8 mm
