abbyniewchas/heart_valve_bioreactor/designs/Full System CAD/Tubing and fittings/flow reg to MR.SLDPRT

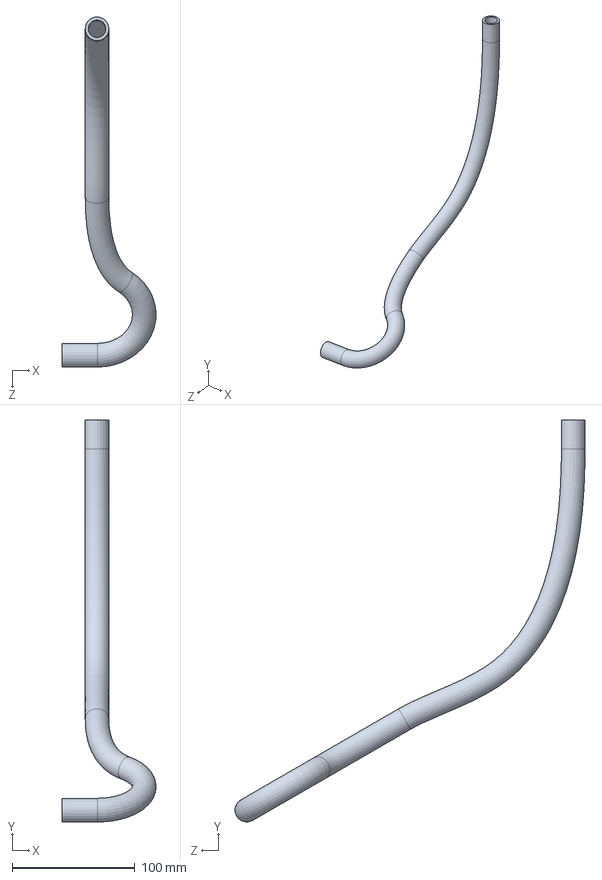
[picture p86: CAD file, 2020-04-21]
designs/Full System CAD/Tubing and fittings/flow reg to MR.SLDPRT
76.6 x 327.2 x 285.0 mm
