abbyniewchas/heart_valve_bioreactor/designs/Full System CAD/Frame/80_20 23in.SLDPRT

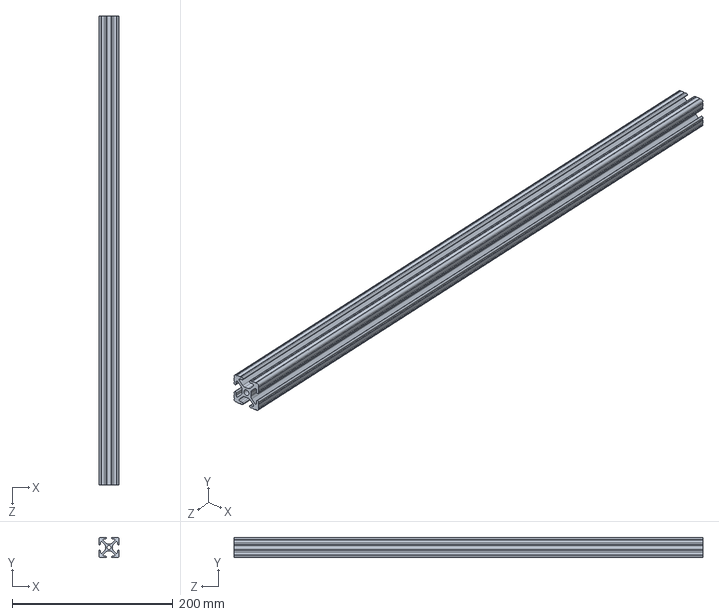
[picture p87: CAD file, 2020-04-21]
designs/Full System CAD/Frame/80_20 23in.SLDPRT
25.4 x 25.4 x 584.2 mm
