abbyniewchas/heart_valve_bioreactor/designs/Full System CAD/Pump redesign concept/redesigned pump piston rack + paddle.SLDPRT

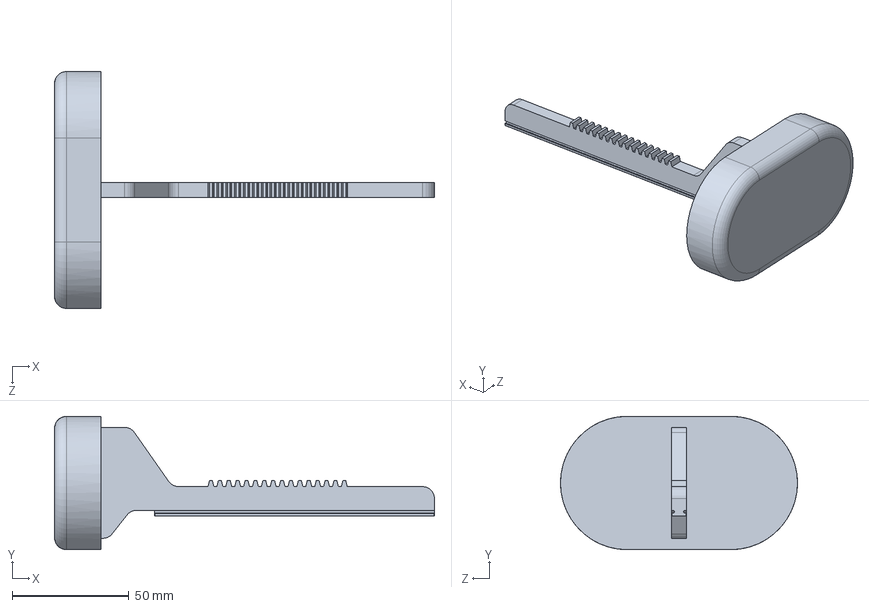
[picture p88: CAD file, 2020-04-21]
designs/Full System CAD/Pump redesign concept/redesigned pump piston rack + paddle.SLDPRT
162.9 x 57.2 x 101.6 mm
