abbyniewchas/heart_valve_bioreactor/designs/Full System CAD/Frame/CC Mount redesign pt 1.SLDPRT

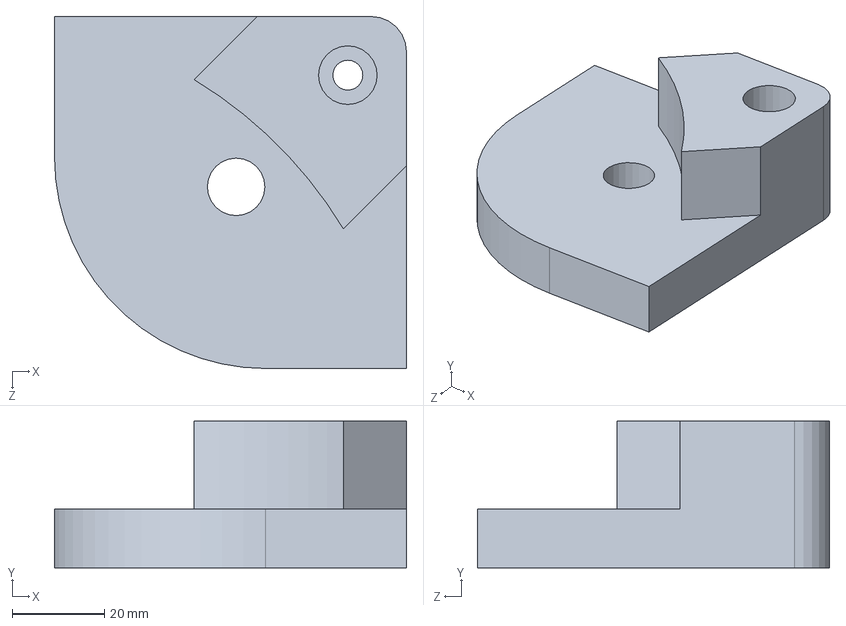
[picture p89: CAD file, 2020-04-21]
designs/Full System CAD/Frame/CC Mount redesign pt 1.SLDPRT
76.2 x 31.8 x 76.2 mm
