abbyniewchas/heart_valve_bioreactor/designs/Full System CAD/Current pump/Pump piston rack.SLDPRT

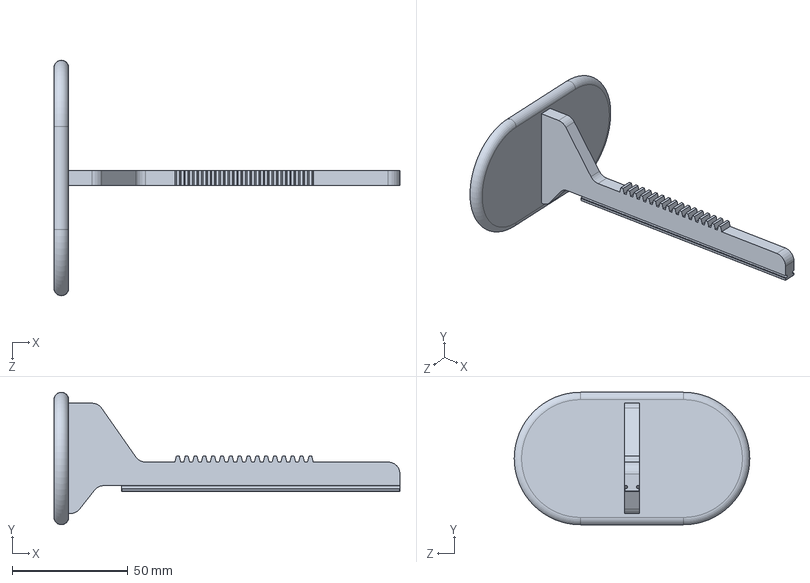
[picture p90: CAD file, 2020-04-21]
designs/Full System CAD/Current pump/Pump piston rack.SLDPRT
149.2 x 57.2 x 101.6 mm
