abbyniewchas/heart_valve_bioreactor/designs/Full System CAD/Frame/80_20 11in.SLDPRT

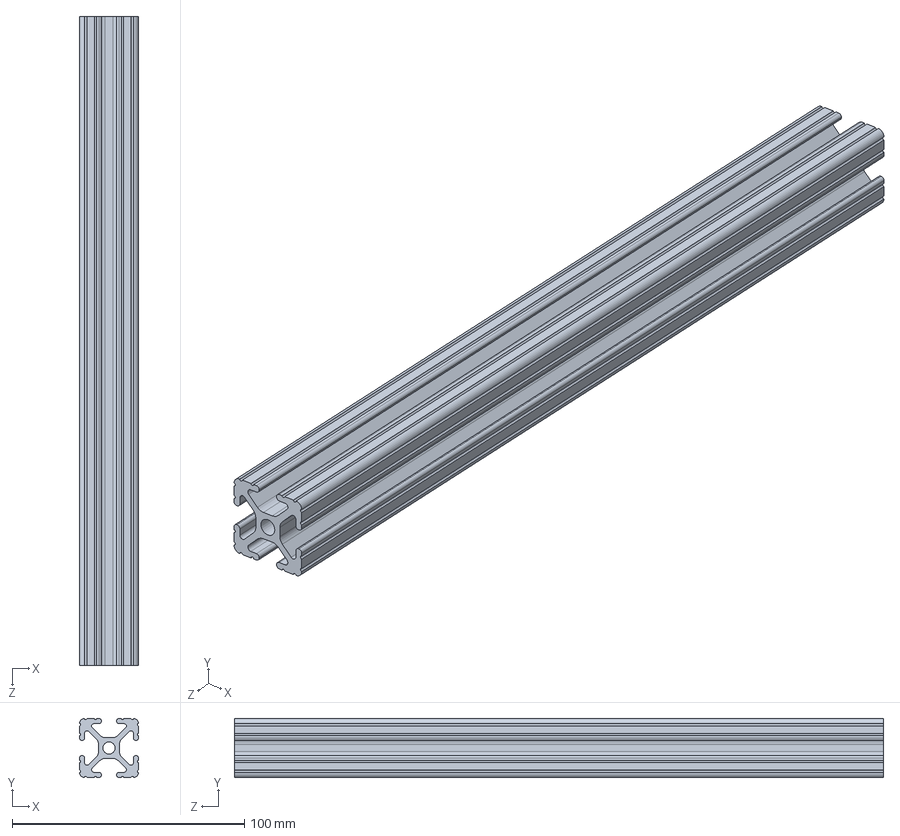
[picture p91: CAD file, 2020-04-21]
designs/Full System CAD/Frame/80_20 11in.SLDPRT
25.4 x 25.4 x 279.4 mm
