abbyniewchas/heart_valve_bioreactor/designs/Full System CAD/Tubing and fittings/PT to PC.SLDPRT

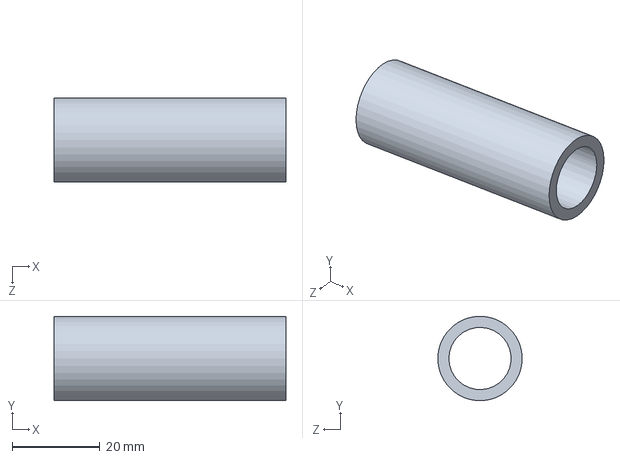
[picture p92: CAD file, 2020-04-21]
designs/Full System CAD/Tubing and fittings/PT to PC.SLDPRT
53.0 x 19.3 x 19.3 mm
