abbyniewchas/heart_valve_bioreactor/designs/Full System CAD/Frame/80_20 L Bracket long.SLDPRT

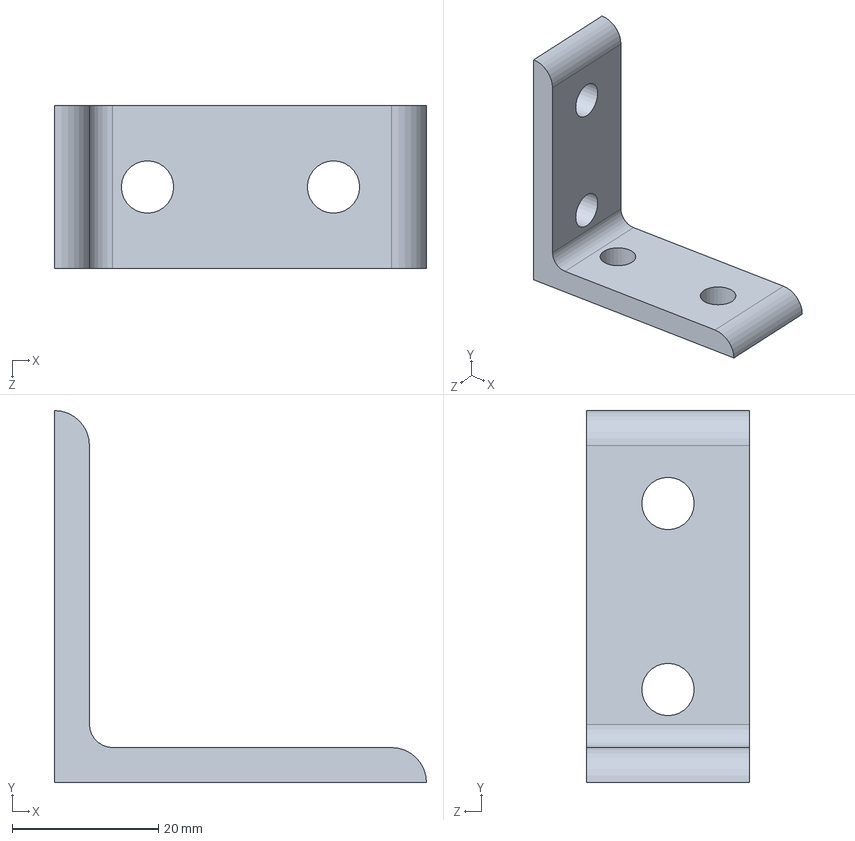
[picture p93: CAD file, 2020-04-21]
designs/Full System CAD/Frame/80_20 L Bracket long.SLDPRT
50.8 x 50.8 x 22.2 mm
