abbyniewchas/heart_valve_bioreactor/designs/Full System CAD/Tubing and fittings/CC to flow reg.SLDPRT

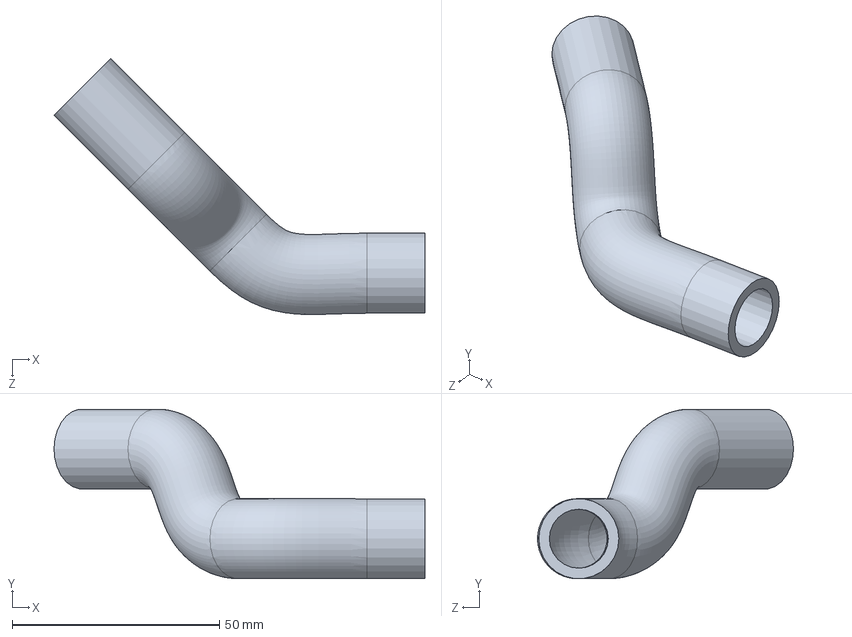
[picture p94: CAD file, 2020-04-21]
designs/Full System CAD/Tubing and fittings/CC to flow reg.SLDPRT
89.4 x 40.9 x 61.7 mm
