abbyniewchas/heart_valve_bioreactor/designs/Full System CAD/Current pump/Pump membrane front.SLDPRT

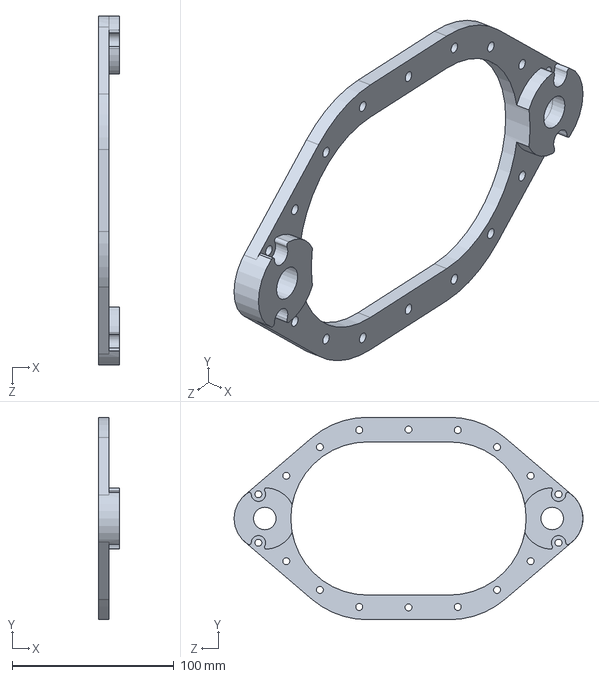
[picture p95: CAD file, 2020-04-21]
designs/Full System CAD/Current pump/Pump membrane front.SLDPRT
12.7 x 125.2 x 215.9 mm
