abbyniewchas/heart_valve_bioreactor/designs/Full System CAD/Frame/80_20 6in.SLDPRT

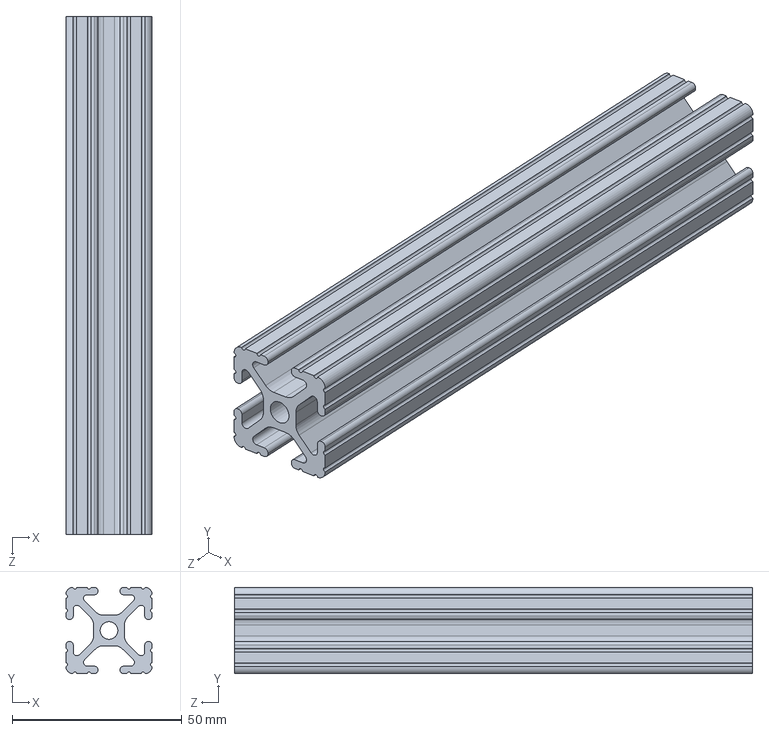
[picture p96: CAD file, 2020-04-21]
designs/Full System CAD/Frame/80_20 6in.SLDPRT
25.4 x 25.4 x 152.4 mm
