abbyniewchas/heart_valve_bioreactor/designs/Full System CAD/Tubing and fittings/half NPT to half in tube.SLDPRT

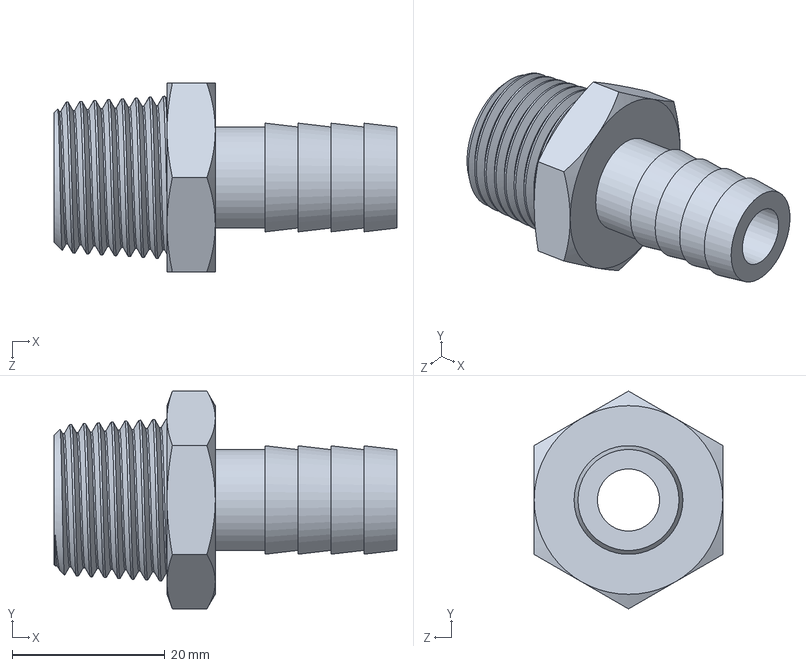
[picture p97: CAD file, 2020-04-21]
designs/Full System CAD/Tubing and fittings/half NPT to half in tube.SLDPRT
44.9 x 28.5 x 24.7 mm
