abbyniewchas/heart_valve_bioreactor/designs/Full System CAD/Tubing and fittings/Checkk-ALL check valve.SLDPRT

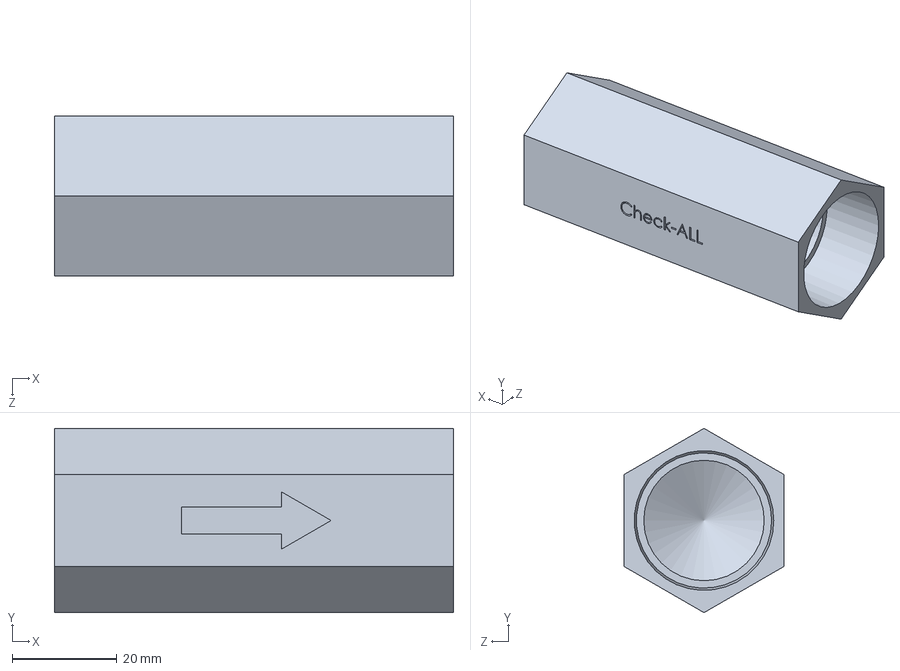
[picture p99: CAD file, 2020-04-21]
designs/Full System CAD/Tubing and fittings/Checkk-ALL check valve.SLDPRT
76.2 x 35.2 x 30.5 mm
