abbyniewchas/heart_valve_bioreactor/designs/Full System CAD/Pump redesign concept/redesigned pump membrane.SLDPRT

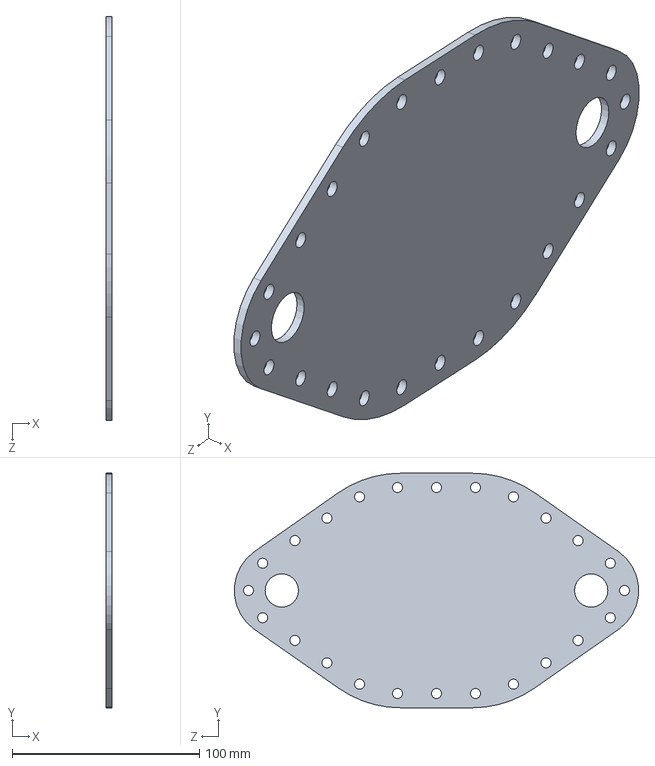
[picture p100: CAD file, 2020-04-21]
designs/Full System CAD/Pump redesign concept/redesigned pump membrane.SLDPRT
3.05 x 125.2 x 215.6 mm
