abbyniewchas/heart_valve_bioreactor/designs/Full System CAD/Tubing and fittings/MR to check valve.SLDPRT

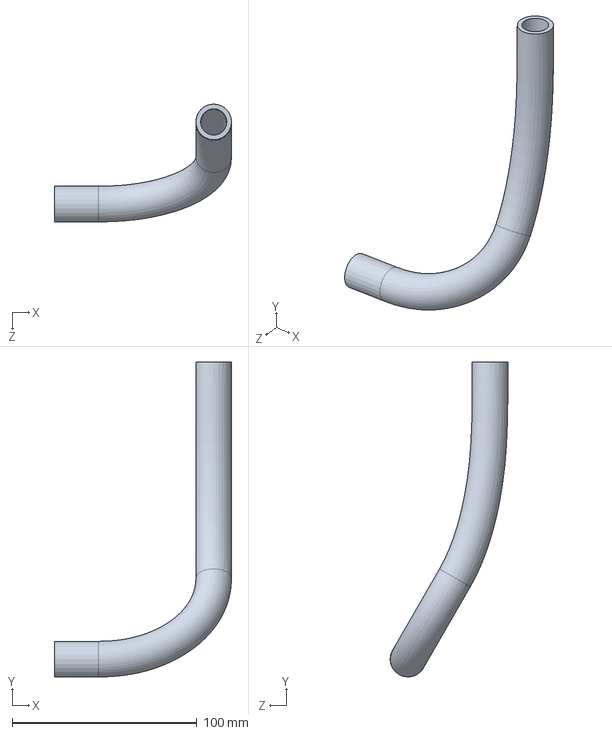
[picture p101: CAD file, 2020-04-21]
designs/Full System CAD/Tubing and fittings/MR to check valve.SLDPRT
95.8 x 170.4 x 63.7 mm
