abbyniewchas/heart_valve_bioreactor/designs/Full System CAD/Frame/80_20 3.75in.SLDPRT

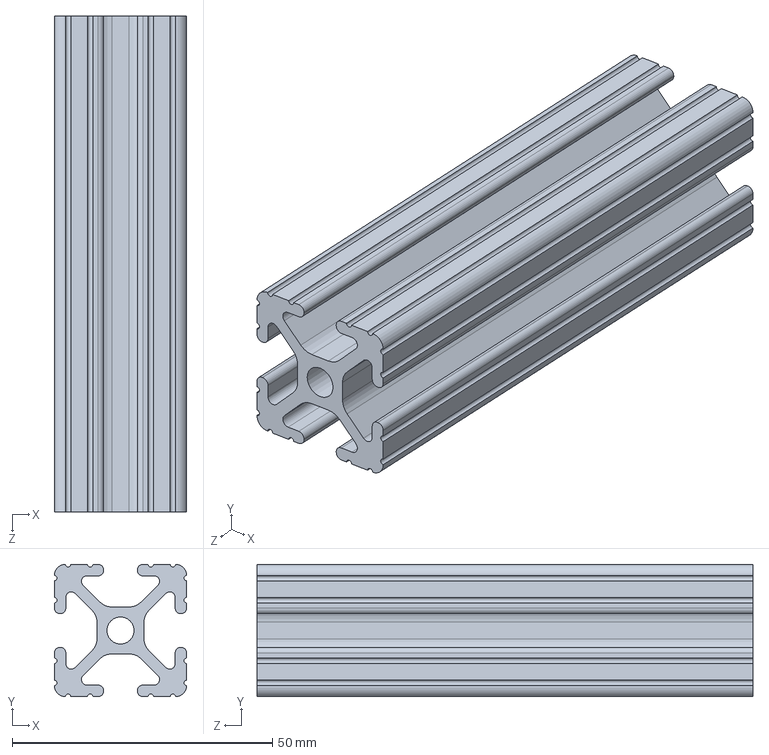
[picture p102: CAD file, 2020-04-21]
designs/Full System CAD/Frame/80_20 3.75in.SLDPRT
25.4 x 25.4 x 95.2 mm
