abbyniewchas/heart_valve_bioreactor/designs/Full System CAD/Pump redesign concept/redesigned membrane front.SLDPRT

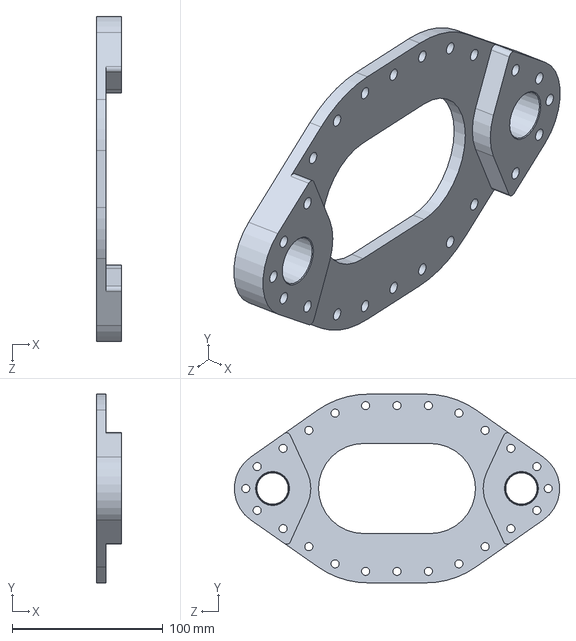
[picture p103: CAD file, 2020-04-21]
designs/Full System CAD/Pump redesign concept/redesigned membrane front.SLDPRT
16.5 x 125.2 x 215.6 mm
