abbyniewchas/heart_valve_bioreactor/designs/Full System CAD/Frame/Flow regulator.SLDPRT

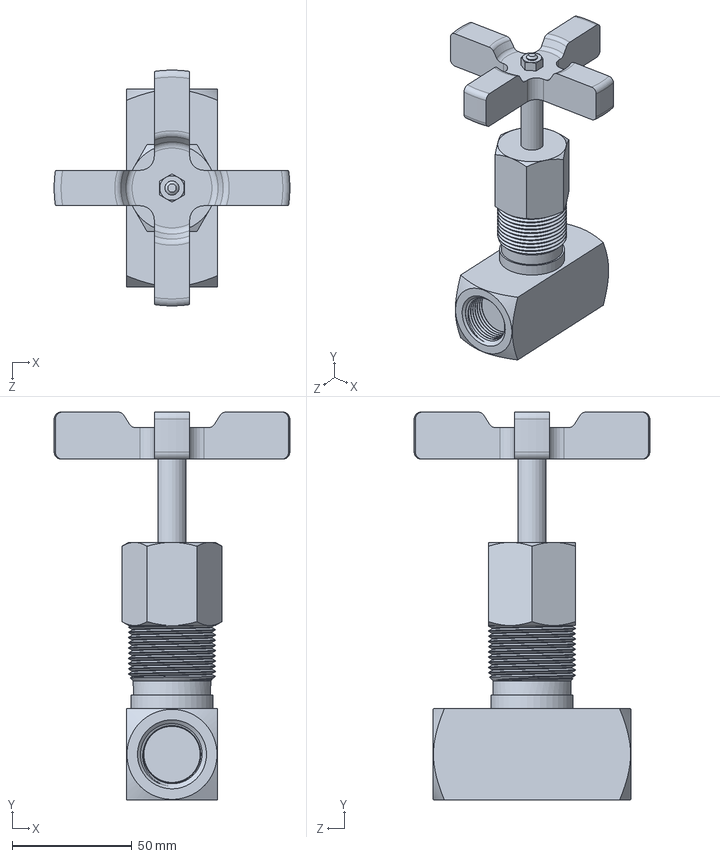
[picture p104: CAD file, 2020-04-21]
designs/Full System CAD/Frame/Flow regulator.SLDPRT
98.4 x 161.9 x 98.4 mm
