abbyniewchas/heart_valve_bioreactor/designs/Full System CAD/Frame/80_20 double 3.5in.SLDPRT

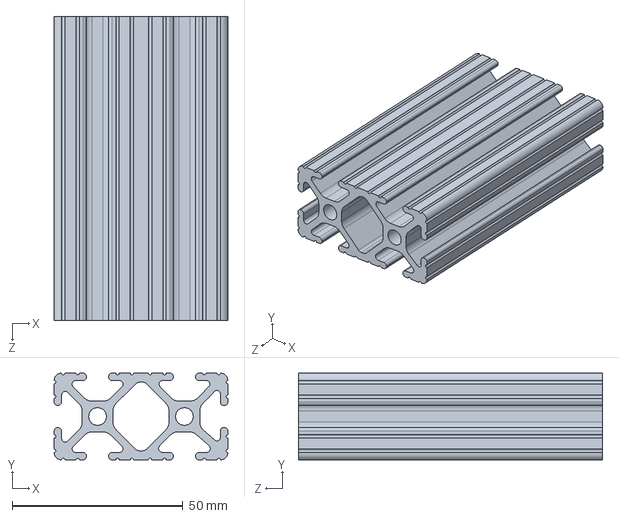
[picture p105: CAD file, 2020-04-21]
designs/Full System CAD/Frame/80_20 double 3.5in.SLDPRT
50.8 x 25.4 x 88.9 mm
