abbyniewchas/heart_valve_bioreactor/designs/Full System CAD/Frame/80_20 8.5in.SLDPRT

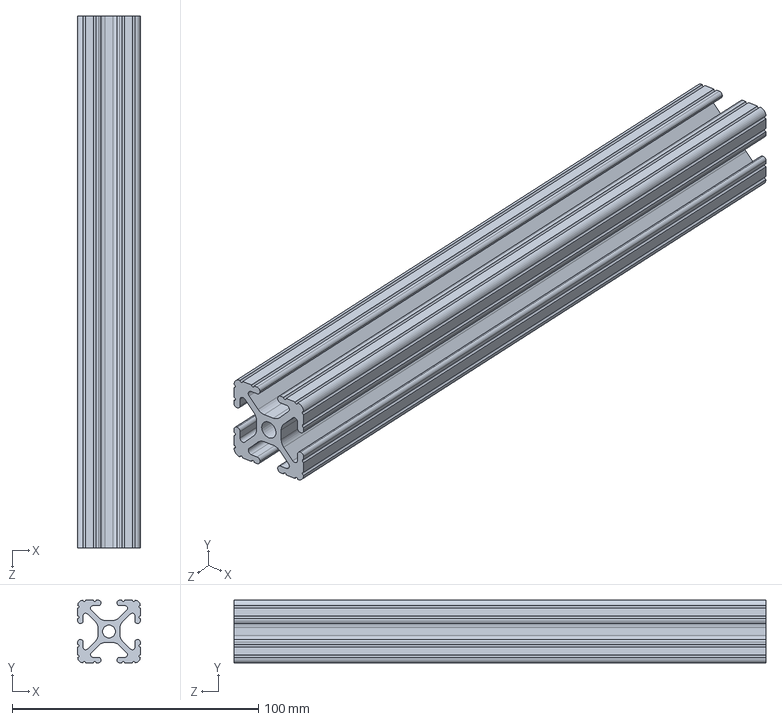
[picture p106: CAD file, 2020-04-21]
designs/Full System CAD/Frame/80_20 8.5in.SLDPRT
25.4 x 25.4 x 215.9 mm
