abbyniewchas/heart_valve_bioreactor/designs/Full System CAD/Frame/CC Mount.SLDPRT

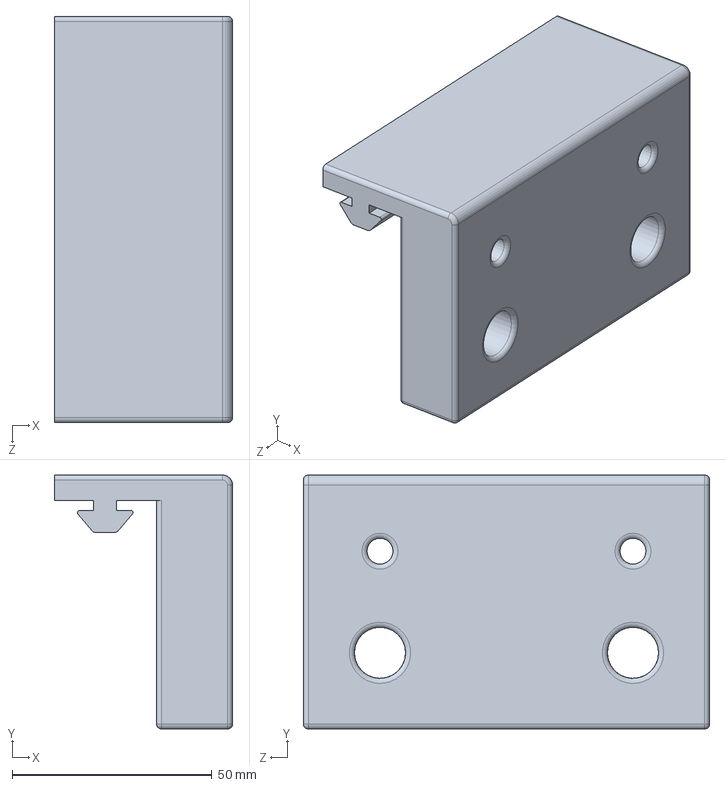
[picture p107: CAD file, 2020-04-21]
designs/Full System CAD/Frame/CC Mount.SLDPRT
44.6 x 63.5 x 101.6 mm
