abbyniewchas/heart_valve_bioreactor/designs/Full System CAD/Frame/80_20 L bracket wide.SLDPRT

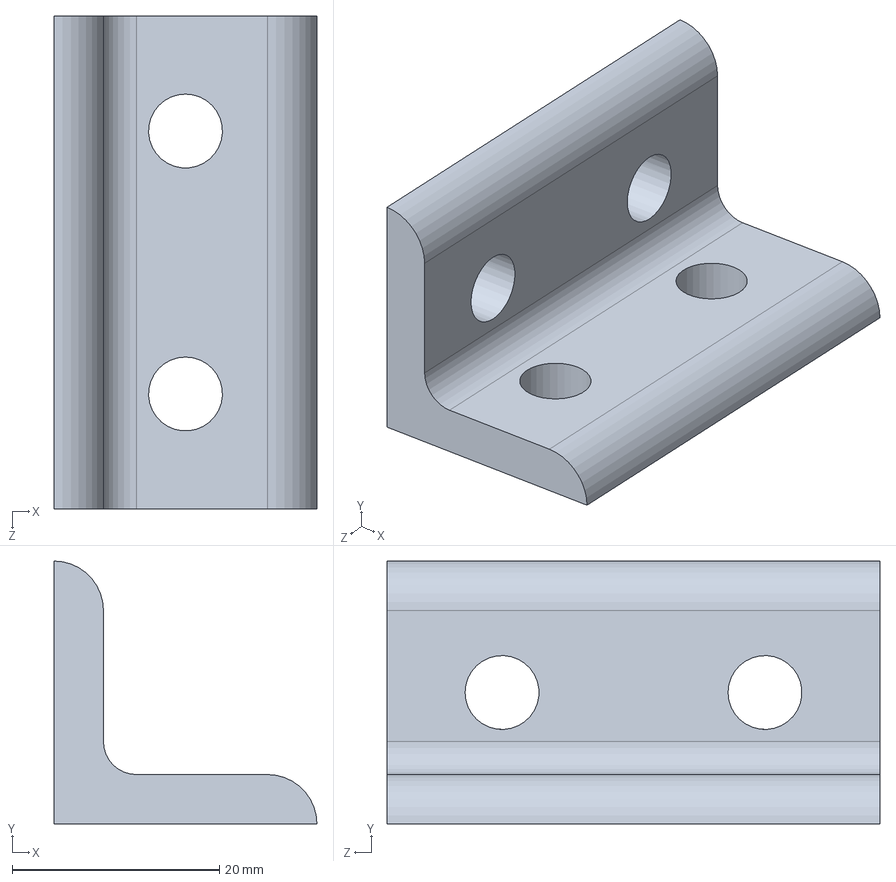
[picture p108: CAD file, 2020-04-21]
designs/Full System CAD/Frame/80_20 L bracket wide.SLDPRT
25.4 x 25.4 x 47.6 mm
