abbyniewchas/heart_valve_bioreactor/designs/Full System CAD/Frame/pump acrylic aligner.SLDPRT

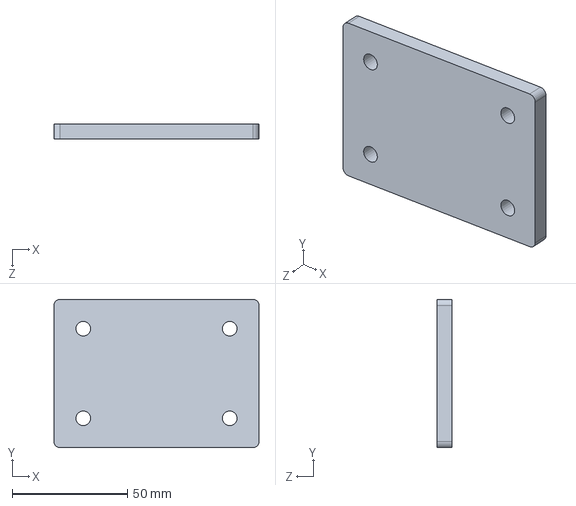
[picture p109: CAD file, 2020-04-21]
designs/Full System CAD/Frame/pump acrylic aligner.SLDPRT
88.9 x 64.3 x 6.35 mm
