abbyniewchas/heart_valve_bioreactor/designs/Full System CAD/Frame/80_20 18.5in.SLDPRT

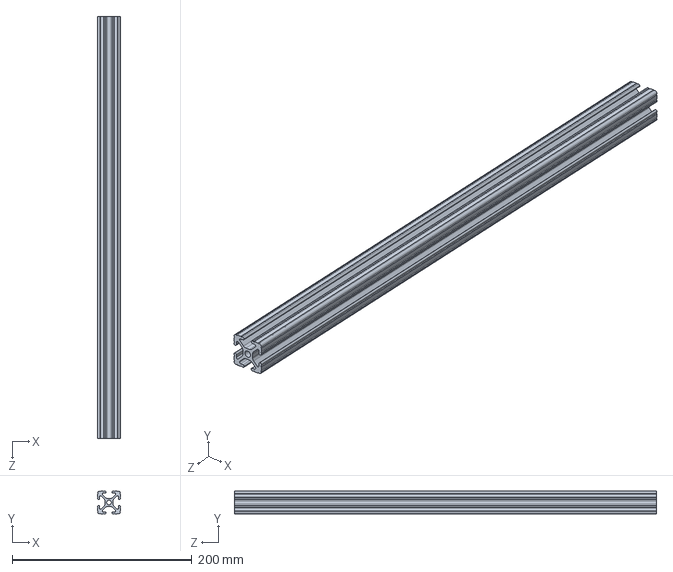
[picture p110: CAD file, 2020-04-21]
designs/Full System CAD/Frame/80_20 18.5in.SLDPRT
25.4 x 25.4 x 469.9 mm
