abbyniewchas/heart_valve_bioreactor/designs/Full System CAD/Frame/CC Mount redesign pt 2.SLDPRT

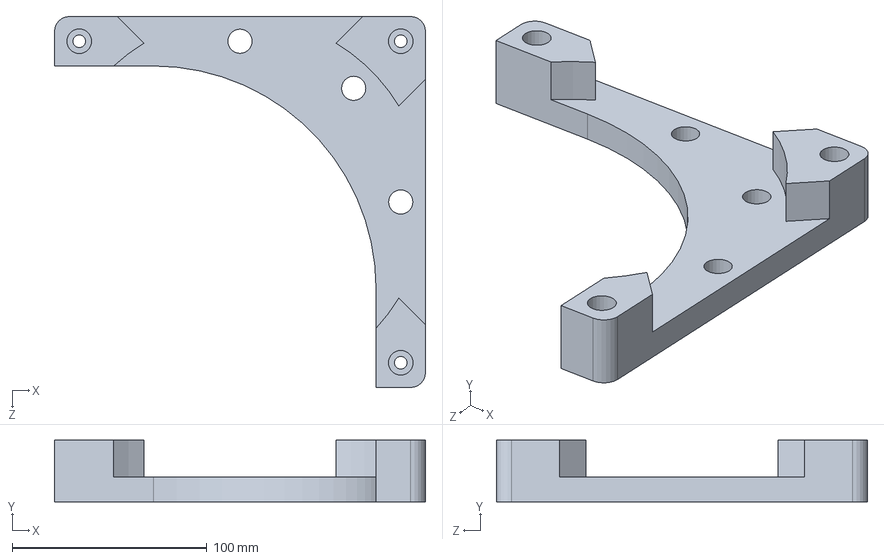
[picture p111: CAD file, 2020-04-21]
designs/Full System CAD/Frame/CC Mount redesign pt 2.SLDPRT
190.5 x 31.8 x 190.5 mm
