abbyniewchas/heart_valve_bioreactor/designs/Full System CAD/Frame/80_20 14in.SLDPRT

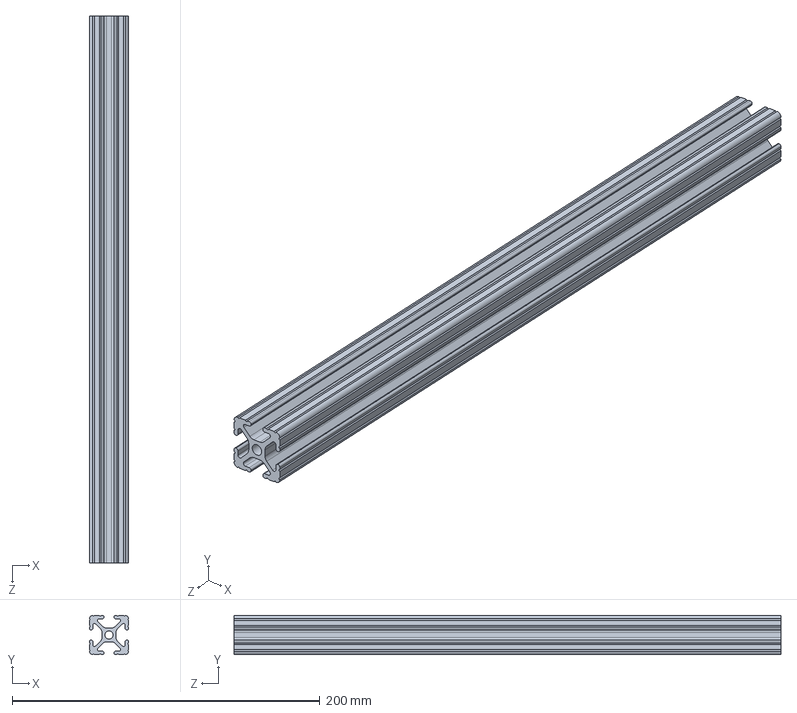
[picture p112: CAD file, 2020-04-21]
designs/Full System CAD/Frame/80_20 14in.SLDPRT
25.4 x 25.4 x 355.6 mm
