abbyniewchas/heart_valve_bioreactor/designs/Full System CAD/Frame/Pump membrane mock-up.SLDPRT

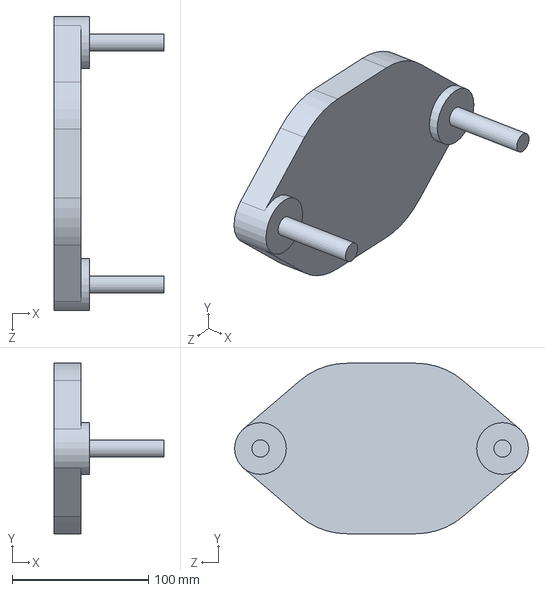
[picture p113: CAD file, 2020-04-21]
designs/Full System CAD/Frame/Pump membrane mock-up.SLDPRT
80.5 x 125.2 x 215.9 mm
